campy/P3Steel-MGN-V19-XL/P3Steel XL MGN V19/P3Steel MGN XL/Piezas impresas/LCD Cajas/Duet 5 Pulgadas/Ensamblaje-Duet5.SLDASM

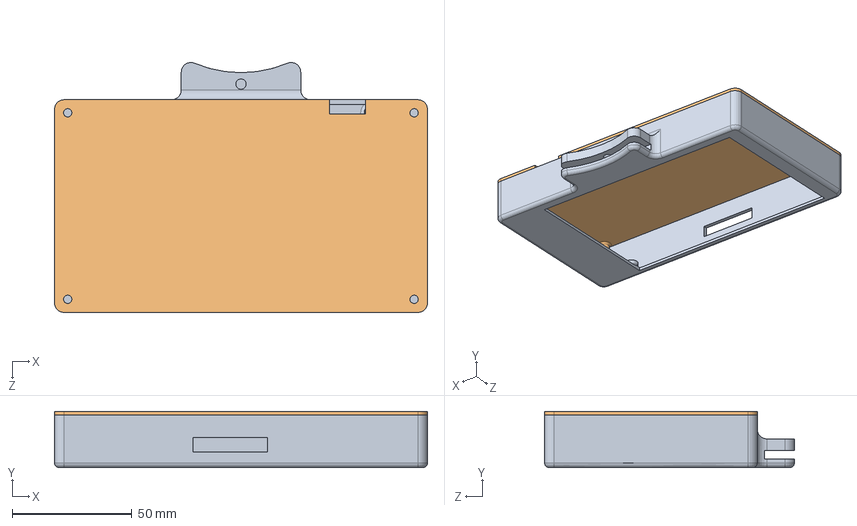
[picture p33: CAD file, 2019-11-12]
P3Steel XL MGN V19/P3Steel MGN XL/Piezas impresas/LCD Cajas/Duet 5 Pulgadas/Ensamblaje-Duet5.SLDASM
156.0 x 23.5 x 104.5 mm
Caja-Duet5
TapaCaja duet 5
