campy/P3Steel-MGN-V19-XL/P3Steel XL MGN V19/P3Steel MGN XL/Source/F688zz/F688ZZ_assembly.SLDASM

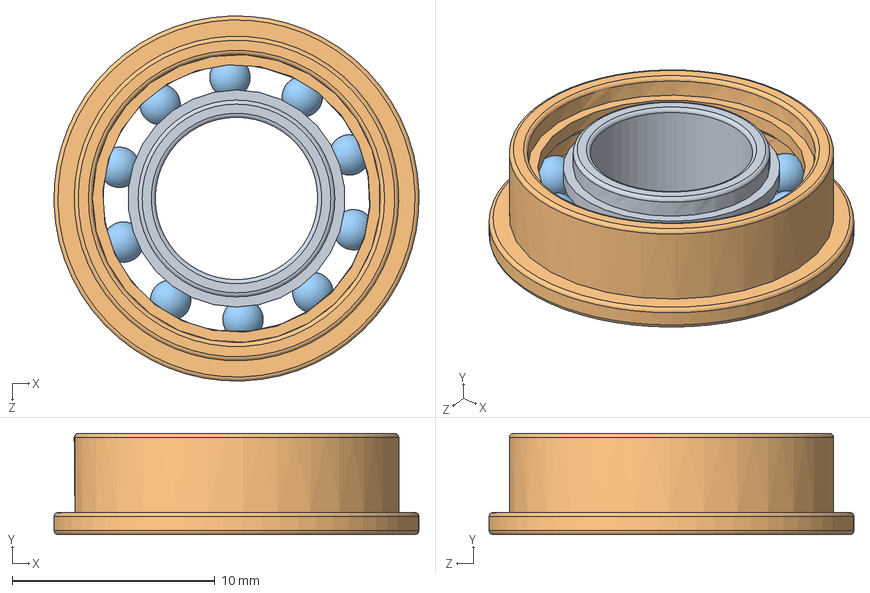
[picture p34: CAD file, 2019-07-11]
P3Steel XL MGN V19/P3Steel MGN XL/Source/F688zz/F688ZZ_assembly.SLDASM
18.0 x 5.00 x 18.0 mm
F688ZZ_shaft
F688ZZ_Housing
F688ZZ_Ball x 10
