campy/P3Steel-MGN-V19-XL/P3Steel XL MGN V19/P3Steel MGN XL/Source/Inductive Sensor/LJ12A3-4-Z.SLDASM

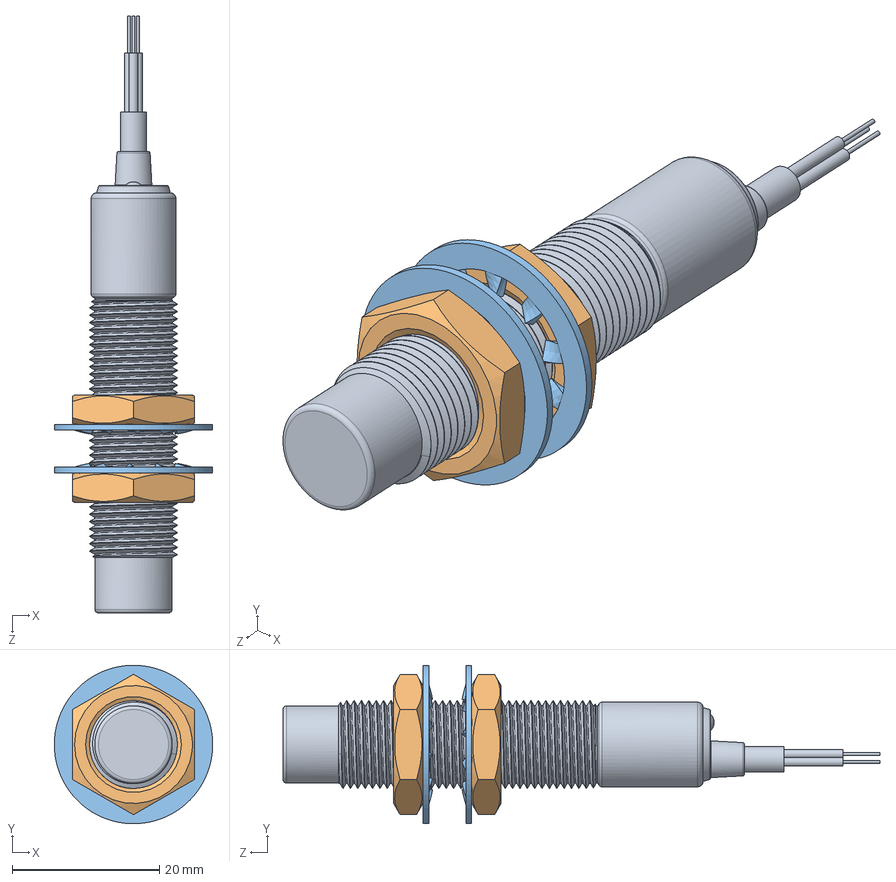
[picture p35: CAD file, 2019-07-11]
P3Steel XL MGN V19/P3Steel MGN XL/Source/Inductive Sensor/LJ12A3-4-Z.SLDASM
21.5 x 21.5 x 81.0 mm
LJ12A3-4-Z
Гайка М12 x 2
Шайба x 2
