campy/P3Steel-MGN-V19-XL/P3Steel XL MGN V19/P3Steel MGN XL/Source/Nema Y/Stepper motor/Nema Z.SLDASM

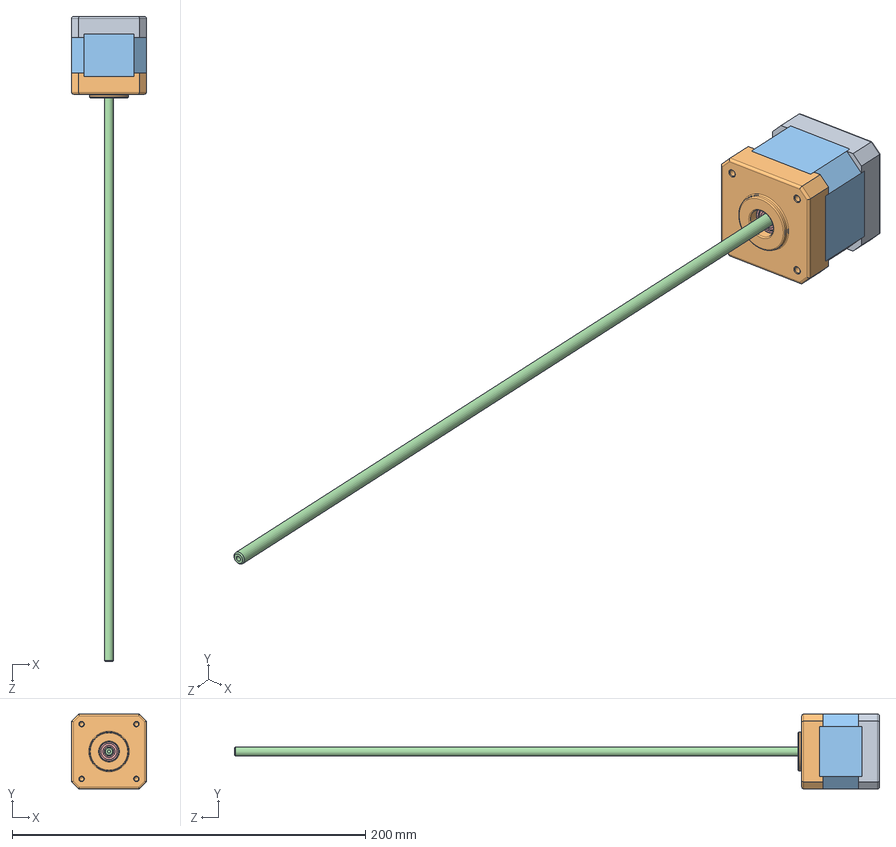
[picture p36: CAD file, 2019-07-11]
P3Steel XL MGN V19/P3Steel MGN XL/Source/Nema Y/Stepper motor/Nema Z.SLDASM
42.3 x 42.3 x 365.0 mm
radial ball bearing_68_iso x 2
pan head cross recess screw_iso x 4
