campy/P3Steel-MGN-V19-XL/P3Steel XL MGN V19/P3Steel MGN XL/Piezas impresas/Cadenetas/Cadeneta 5/Ensamblaje P3steel.SLDASM

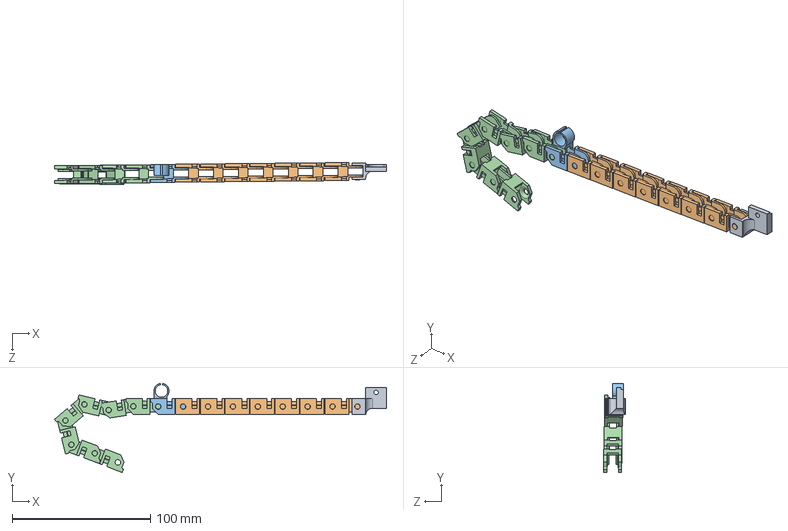
[picture p38: CAD file, 2019-07-11]
P3Steel XL MGN V19/P3Steel MGN XL/Piezas impresas/Cadenetas/Cadeneta 5/Ensamblaje P3steel.SLDASM
240.0 x 64.4 x 15.8 mm
Soporte cama
Eslabon 5 Fijo x 7
Eslabon 5 con soporte
Eslabon 5 Bloqueado x 7
