campy/P3Steel-MGN-V19-XL/P3Steel XL MGN V19/P3Steel MGN XL/Ensamblaje-Xmotor.SLDASM

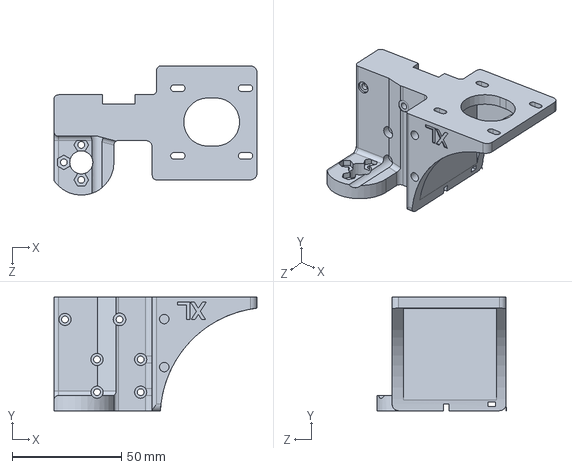
[picture p39: CAD file, 2019-09-07]
P3Steel XL MGN V19/P3Steel MGN XL/Ensamblaje-Xmotor.SLDASM
93.0 x 52.0 x 59.2 mm
