campy/P3Steel-MGN-V19-XL/P3Steel XL MGN V19/P3Steel MGN XL/Extrusor BMG+E3DV6/E3dSimple/fanduct.SLDASM

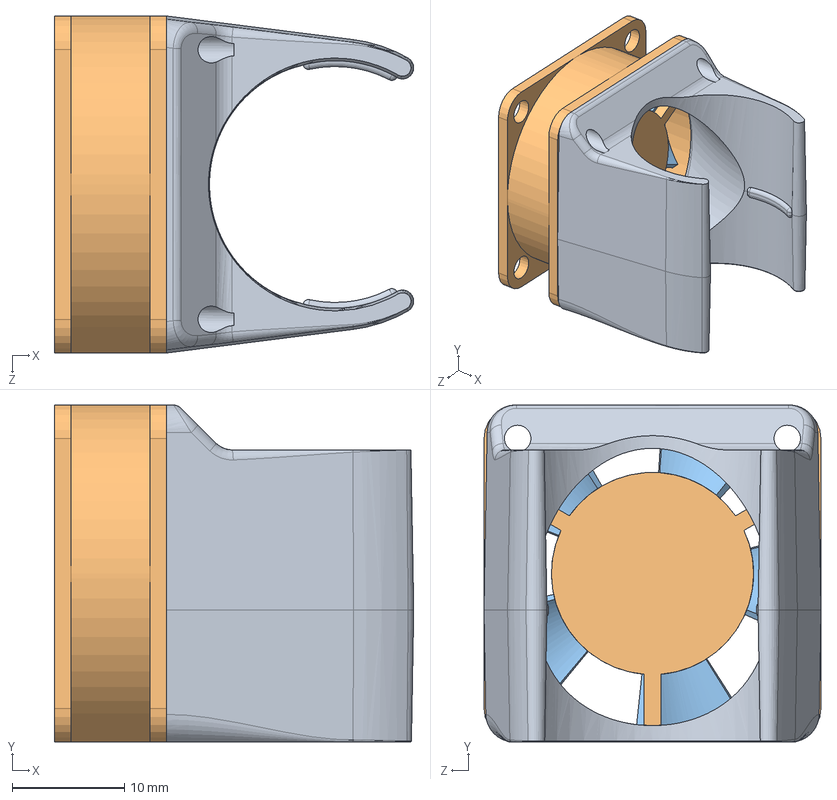
[picture p40: CAD file, 2019-09-07]
P3Steel XL MGN V19/P3Steel MGN XL/Extrusor BMG+E3DV6/E3dSimple/fanduct.SLDASM
32.0 x 30.0 x 30.0 mm
fan duct
fan sub1
fan sub2
