campy/P3Steel-MGN-V19-XL/P3Steel XL MGN V19/P3Steel MGN XL/Piezas impresas/Cadenetas/Cadeneta 15/Ensamblaje Eslabon 15.SLDASM

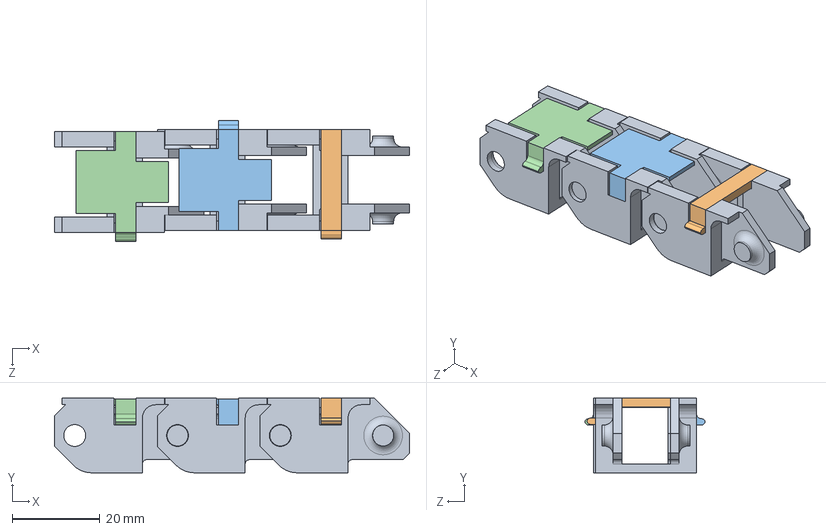
[picture p41: CAD file, 2019-07-11]
P3Steel XL MGN V19/P3Steel MGN XL/Piezas impresas/Cadenetas/Cadeneta 15/Ensamblaje Eslabon 15.SLDASM
80.8 x 17.0 x 27.4 mm
Eslabon 15 x 3
Cierre 15
Cierre 15 Tapa R
Cierre 15 Tapa L
