campy/P3Steel-MGN-V19-XL/P3Steel XL MGN V19/P3Steel MGN XL/Piezas impresas/Cadenetas/Cadeneta 5/Ensamblaje Eslobones.SLDASM

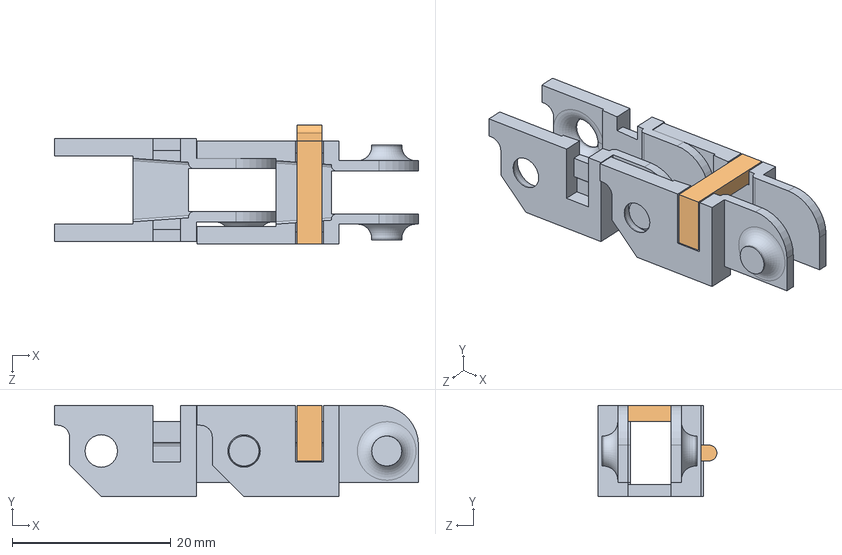
[picture p42: CAD file, 2019-07-11]
P3Steel XL MGN V19/P3Steel MGN XL/Piezas impresas/Cadenetas/Cadeneta 5/Ensamblaje Eslobones.SLDASM
45.9 x 11.5 x 15.0 mm
Eslabon 5 Bloqueado x 2
Cierre 5
