campy/P3Steel-MGN-V19-XL/P3Steel XL MGN V19/P3Steel MGN XL/Piezas impresas/Cadenetas/Cadeneta 5/EnsamblajeBandejaY.SLDASM

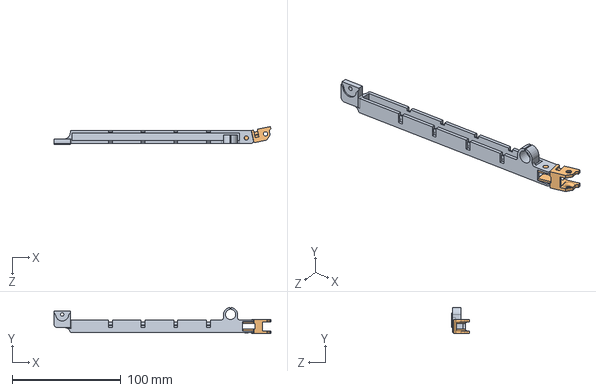
[picture p44: CAD file, 2019-07-11]
P3Steel XL MGN V19/P3Steel MGN XL/Piezas impresas/Cadenetas/Cadeneta 5/EnsamblajeBandejaY.SLDASM
199.1 x 23.9 x 16.5 mm
Soporte Base V2
Eslabon 5 Bloqueado
