campy/P3Steel-MGN-V19-XL/P3Steel XL MGN V19/P3Steel MGN XL/Source/MGN12/MGN12-450.SLDASM

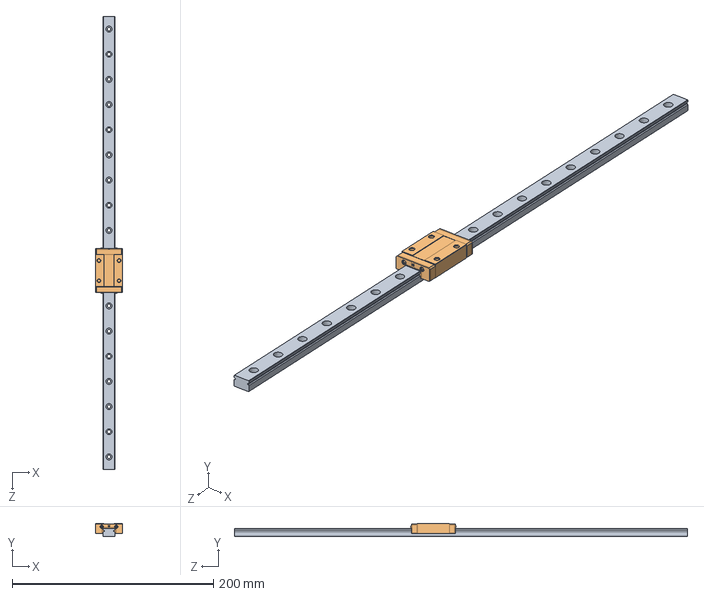
[picture p45: CAD file, 2019-07-11]
P3Steel XL MGN V19/P3Steel MGN XL/Source/MGN12/MGN12-450.SLDASM
27.0 x 13.0 x 450.0 mm
MGN12_450
MGN12-H
