campy/P3Steel-MGN-V19-XL/P3Steel XL MGN V19/P3Steel MGN XL/Source/Titan Aero/Titan Aero P3steel/soportetitan.SLDASM

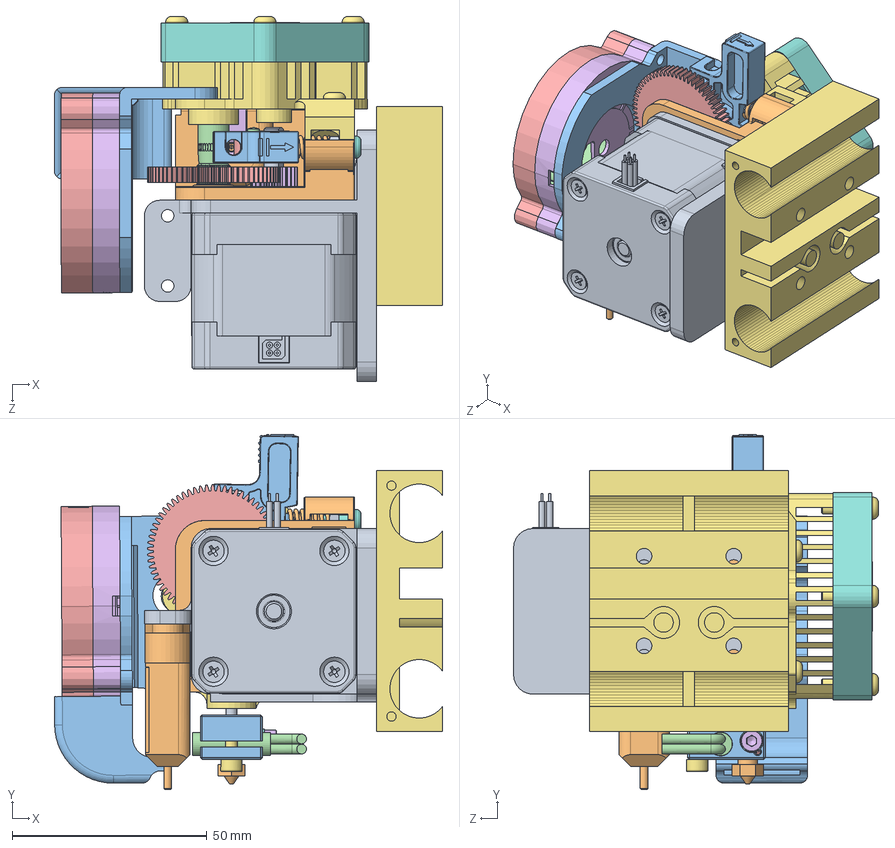
[picture p46: CAD file, 2019-07-11]
P3Steel XL MGN V19/P3Steel MGN XL/Source/Titan Aero/Titan Aero P3steel/soportetitan.SLDASM
99.6 x 91.2 x 93.6 mm
soportetitan
Base
9x5x3mm bearing x 2
hobbed wheel
filament gear
motor gear
cover
m3x8
M3 nut
idler spring
tensioner
idler bearing pin
idler bearing
guide tube
ISO 7380 - M3 x 28 v1 x 8
Fan 40 X 40 X 10 v4
E3D v6 HotEnd - Heatbreak
E3D v6 HotEnd - Nozzle
E3D v6 HotEnd - Heat Block
Ceramic Cartridge Heater
Thermistor
HEXAGON SOCKET HEAD CAP SCREWS_SCB3-4
HEXAGON SOCKET HEAD CAP SCREWS_SCB3-10
Flat Washers_PWF3
17HM15-0904S
BLTouch
tobera5015s
turbine
top
bottom
xcarriage
