campy/P3Steel-MGN-V19-XL/P3Steel XL MGN V19/P3Steel MGN XL/Source/MGN12/17HM15-0904S.SLDASM

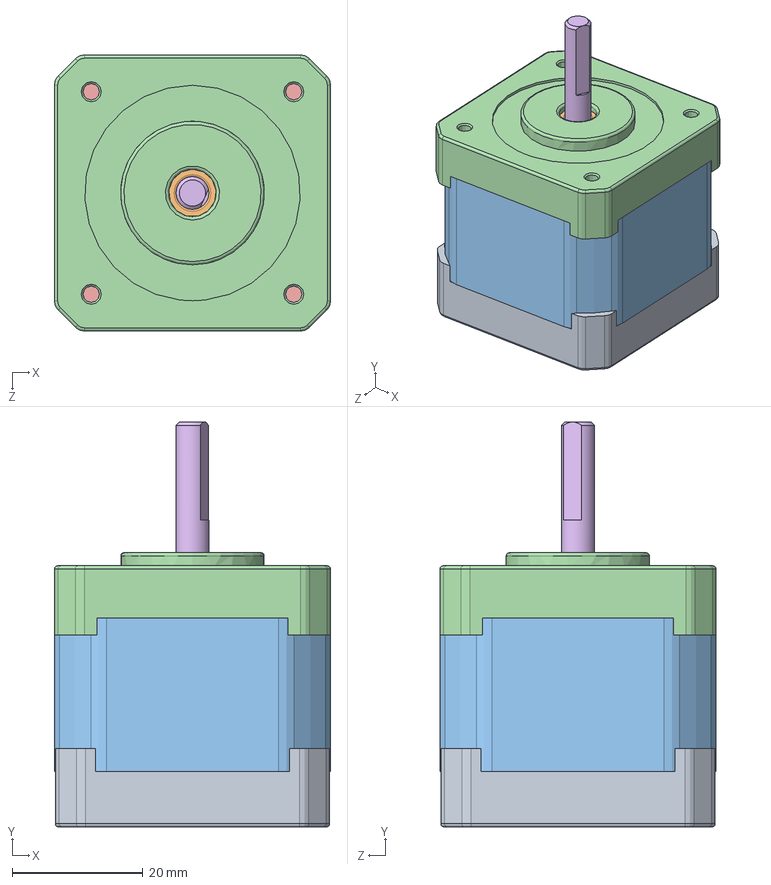
[picture p47: CAD file, 2019-07-11]
P3Steel XL MGN V19/P3Steel MGN XL/Source/MGN12/17HM15-0904S.SLDASM
42.3 x 62.0 x 42.3 mm
nema17_bottom_40mm
radial ball bearing_68_din x 2
nema17_middle_40mm
nema17_top_40mm
countersunk flat head cross recess screw_din x 4
nema17_shaft_40mm
