campy/P3Steel-MGN-V19-XL/P3Steel MGN XL BMG/Piezas impresas/LCD Cajas/Duet 7 Pulgadas/Delantera.STL

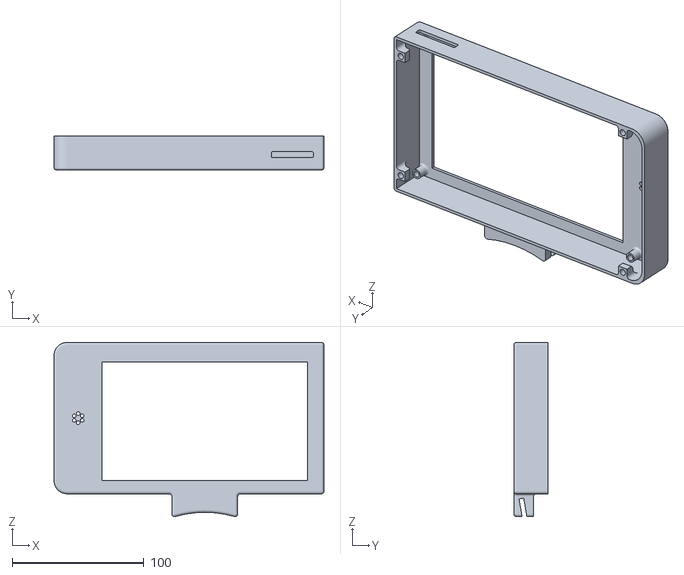
[picture p50: CAD file, 2019-07-11]
P3Steel MGN XL BMG/Piezas impresas/LCD Cajas/Duet 7 Pulgadas/Delantera.STL
205.0 x 26.0 x 132.3
