campy/P3Steel-MGN-V19-XL/P3Steel XL MGN V19/P3Steel MGN XL/Extrusor BMG+E3DV6/E3dSimple/fan sub2.SLDPRT

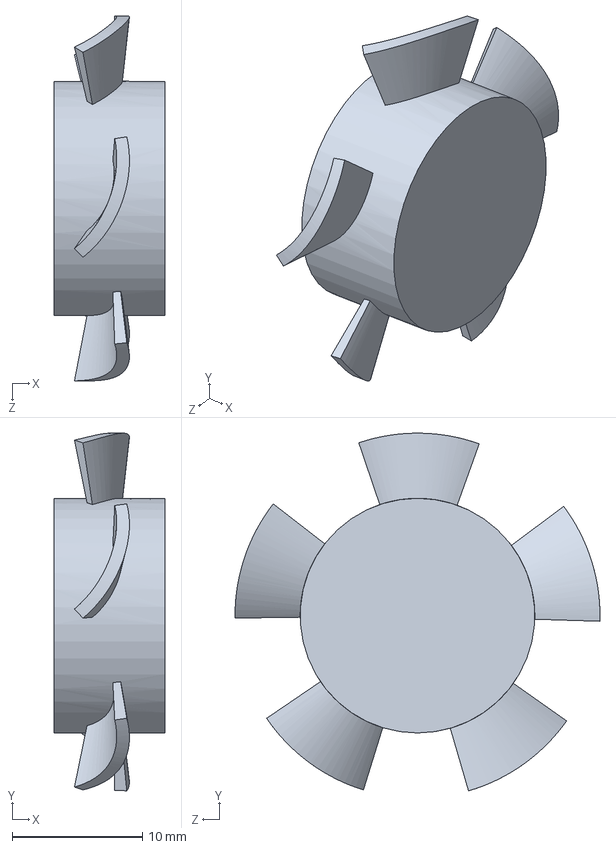
[picture p51: CAD file, 2019-09-07]
P3Steel XL MGN V19/P3Steel MGN XL/Extrusor BMG+E3DV6/E3dSimple/fan sub2.SLDPRT
8.50 x 27.4 x 28.0 mm
