campy/P3Steel-MGN-V19-XL/P3Steel XL MGN V19/P3Steel MGN XL/Extrusor BMG+E3DV6/Nema 17 Corto/Nema 17.SLDPRT

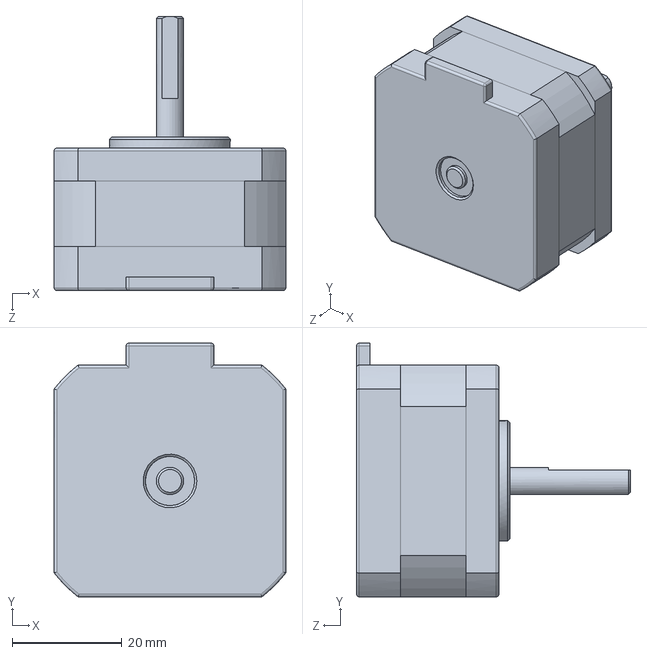
[picture p52: CAD file, 2019-09-07]
P3Steel XL MGN V19/P3Steel MGN XL/Extrusor BMG+E3DV6/Nema 17 Corto/Nema 17.SLDPRT
42.3 x 46.3 x 50.0 mm
