campy/P3Steel-MGN-V19-XL/P3Steel XL MGN V19/P3Steel MGN XL/Extrusor BMG+E3DV6/Radial Cooling Fan 50mm DC12V/top.SLDPRT

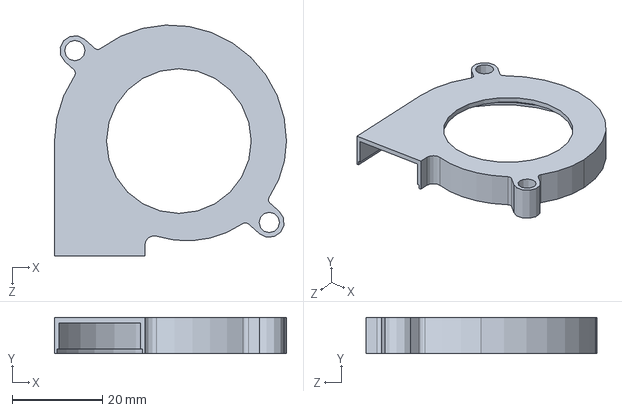
[picture p53: CAD file, 2019-09-07]
P3Steel XL MGN V19/P3Steel MGN XL/Extrusor BMG+E3DV6/Radial Cooling Fan 50mm DC12V/top.SLDPRT
51.3 x 8.00 x 51.0 mm
