campy/P3Steel-MGN-V19-XL/P3Steel XL MGN V19/P3Steel MGN XL/Extrusor BMG+Mosquito/Radial Cooling Fan 50mm DC12V/bottom.SLDPRT

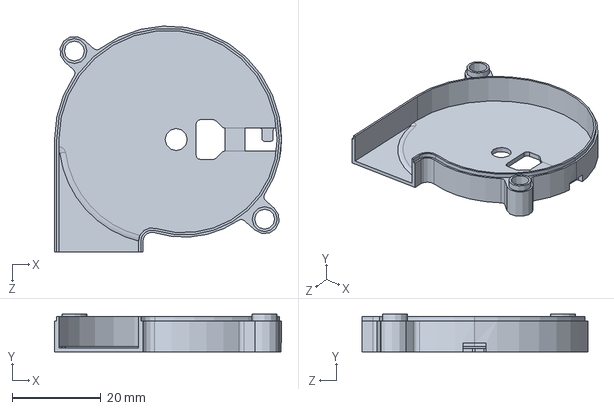
[picture p54: CAD file, 2019-09-07]
P3Steel XL MGN V19/P3Steel MGN XL/Extrusor BMG+Mosquito/Radial Cooling Fan 50mm DC12V/bottom.SLDPRT
51.3 x 8.50 x 51.0 mm
