campy/P3Steel-MGN-V19-XL/P3Steel XL MGN V19/P3Steel MGN XL/Extrusor Titan Aero/Titan Aero/Titan Aero P3steel/Blower titan/Titan_Aero_Shroud_360_Left.stl

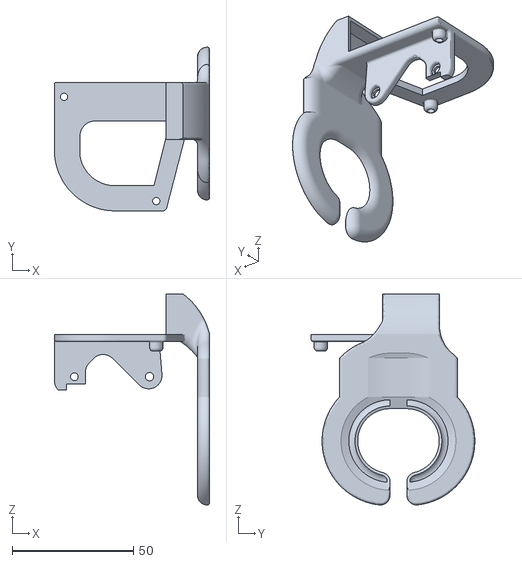
[picture p55: CAD file, 2019-07-11]
P3Steel XL MGN V19/P3Steel MGN XL/Extrusor Titan Aero/Titan Aero/Titan Aero P3steel/Blower titan/Titan_Aero_Shroud_360_Left.stl
64.0 x 67.5 x 87.0
