campy/P3Steel-MGN-V19-XL/P3Steel XL MGN V19/P3Steel MGN XL/Extrusor Titan Aero/X-CarriageV2 Titan.SLDPRT

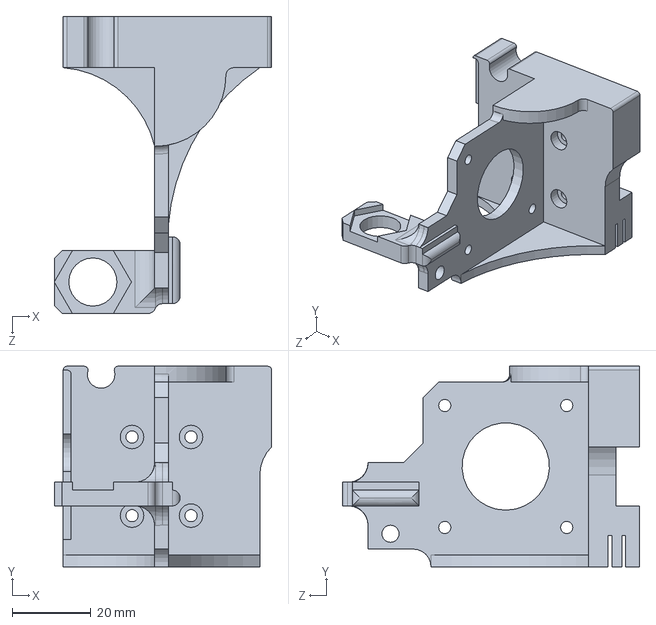
[picture p56: CAD file, 2020-03-17]
P3Steel XL MGN V19/P3Steel MGN XL/Extrusor Titan Aero/X-CarriageV2 Titan.SLDPRT
55.2 x 51.0 x 75.5 mm
