campy/P3Steel-MGN-V19-XL/P3Steel XL MGN V19/P3Steel MGN XL/Marco central XL Offset.SLDPRT

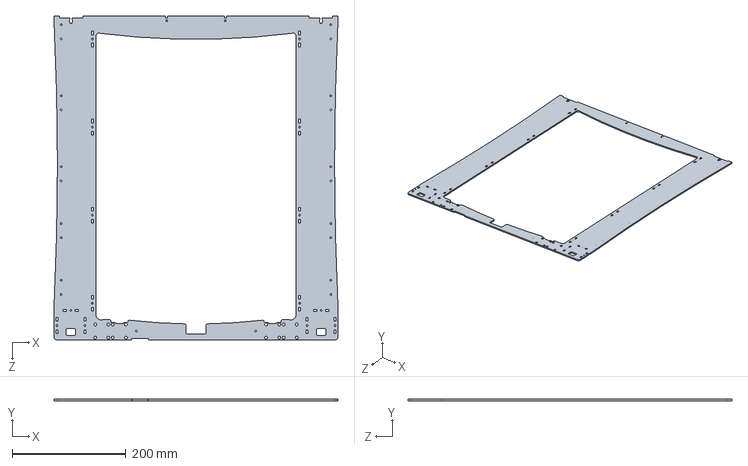
[picture p57: CAD file, 2020-01-10]
P3Steel XL MGN V19/P3Steel MGN XL/Marco central XL Offset.SLDPRT
500.0 x 3.00 x 570.0 mm
