campy/P3Steel-MGN-V19-XL/P3Steel XL MGN V19/P3Steel MGN XL/Piezas impresas/Cadenetas/Cadeneta 15/Otros/Cierre 15.SLDPRT

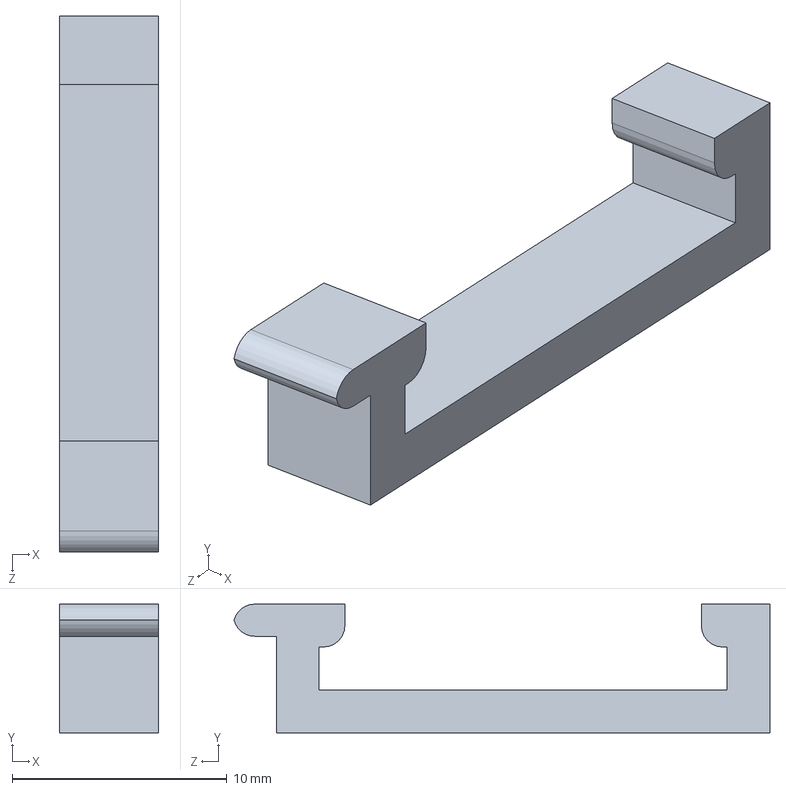
[picture p58: CAD file, 2019-07-11]
P3Steel XL MGN V19/P3Steel MGN XL/Piezas impresas/Cadenetas/Cadeneta 15/Otros/Cierre 15.SLDPRT
4.60 x 6.00 x 25.0 mm
