campy/P3Steel-MGN-V19-XL/P3Steel XL MGN V19/P3Steel MGN XL/Piezas impresas/Cadenetas/Cadeneta 15/Soporte Xcarriage.SLDPRT

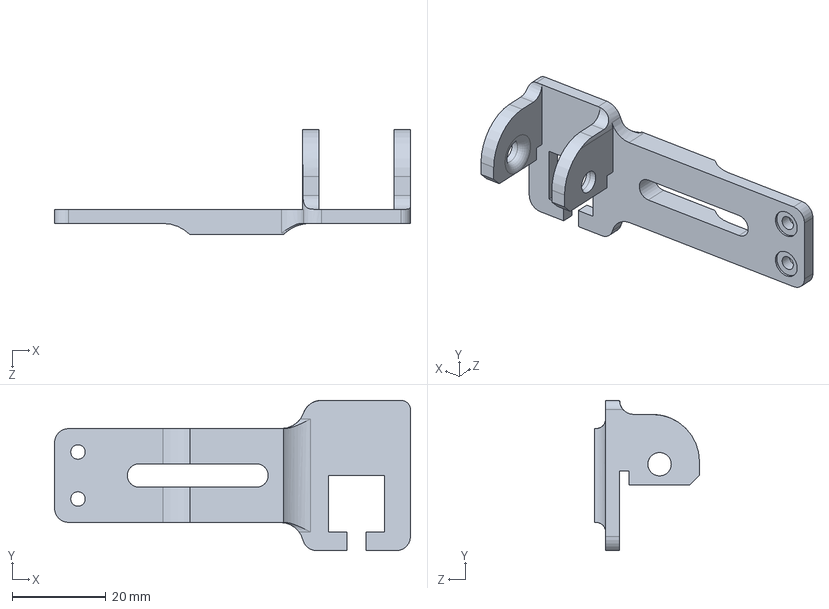
[picture p59: CAD file, 2019-09-07]
P3Steel XL MGN V19/P3Steel MGN XL/Piezas impresas/Cadenetas/Cadeneta 15/Soporte Xcarriage.SLDPRT
75.8 x 32.0 x 22.4 mm
