campy/P3Steel-MGN-V19-XL/P3Steel XL MGN V19/P3Steel MGN XL/Piezas impresas/Cadenetas/Cadeneta 5/Otros Tipos Eslabones/Eslabon 5 Fijo.SLDPRT

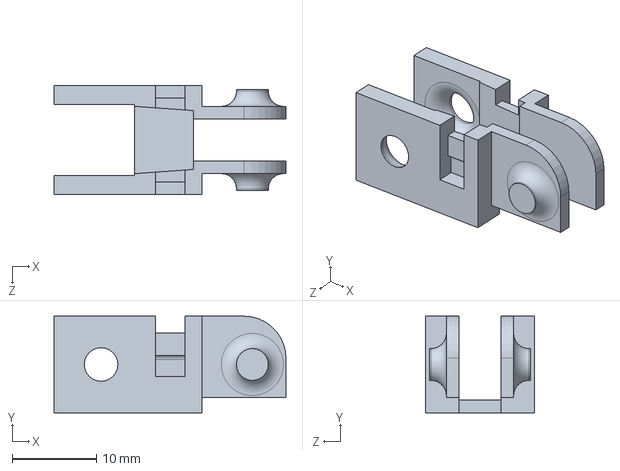
[picture p60: CAD file, 2019-07-11]
P3Steel XL MGN V19/P3Steel MGN XL/Piezas impresas/Cadenetas/Cadeneta 5/Otros Tipos Eslabones/Eslabon 5 Fijo.SLDPRT
27.6 x 11.5 x 13.0 mm
