campy/P3Steel-MGN-V19-XL/P3Steel XL MGN V19/P3Steel MGN XL/Piezas impresas/Cadenetas/Cadeneta 5/Soporte electronica V2.SLDPRT

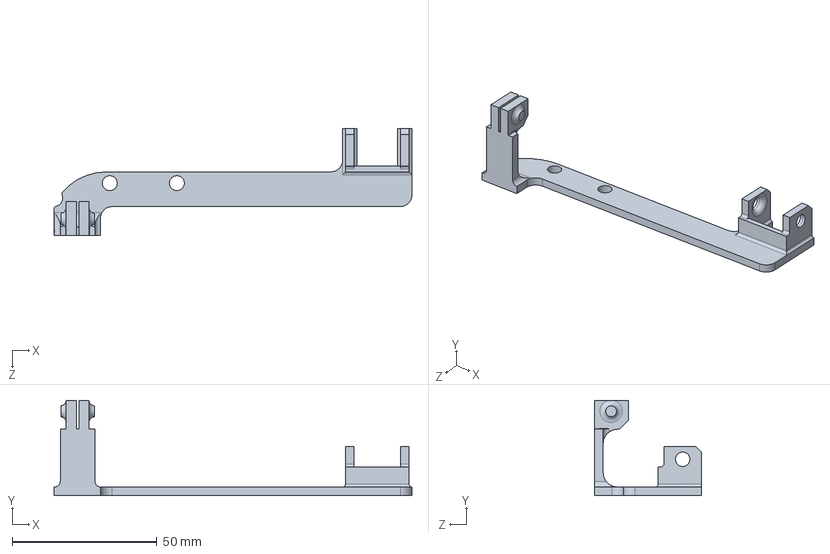
[picture p61: CAD file, 2019-10-11]
P3Steel XL MGN V19/P3Steel MGN XL/Piezas impresas/Cadenetas/Cadeneta 5/Soporte electronica V2.SLDPRT
123.8 x 33.0 x 37.0 mm
