campy/P3Steel-MGN-V19-XL/P3Steel XL MGN V19/P3Steel MGN XL/Piezas impresas/F-Sensor/Sensor con endstop/Soporte F-Sensor.SLDPRT

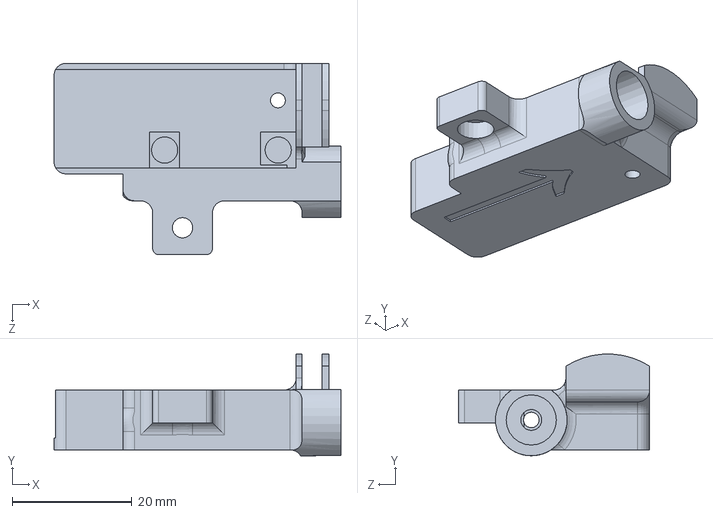
[picture p62: CAD file, 2019-07-11]
P3Steel XL MGN V19/P3Steel MGN XL/Piezas impresas/F-Sensor/Sensor con endstop/Soporte F-Sensor.SLDPRT
48.0 x 17.0 x 32.0 mm
