campy/P3Steel-MGN-V19-XL/P3Steel XL MGN V19/P3Steel MGN XL/Piezas impresas/LCD Cajas/Duet 5 Pulgadas/Caja-Duet5.sldprt

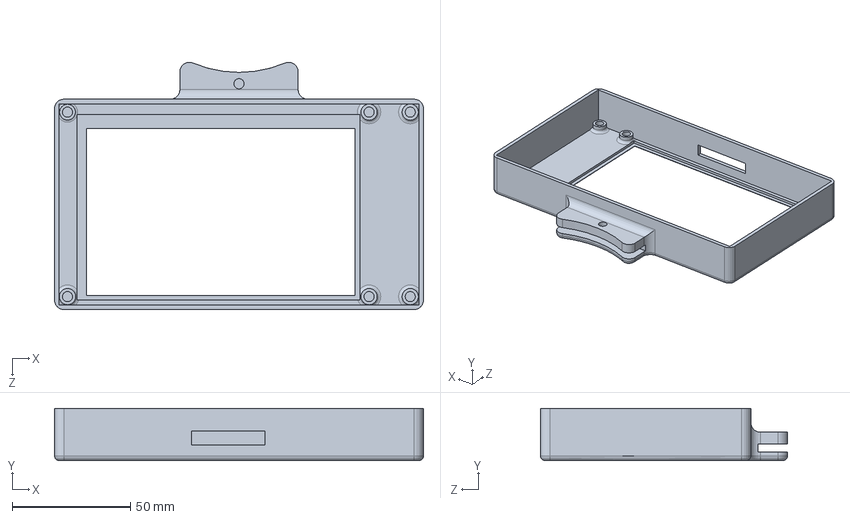
[picture p63: CAD file, 2019-11-12]
P3Steel XL MGN V19/P3Steel MGN XL/Piezas impresas/LCD Cajas/Duet 5 Pulgadas/Caja-Duet5.sldprt
156.0 x 22.0 x 104.5 mm
