campy/P3Steel-MGN-V19-XL/P3Steel XL MGN V19/P3Steel MGN XL/Piezas impresas/LCD Cajas/Grapa LCD2.SLDPRT

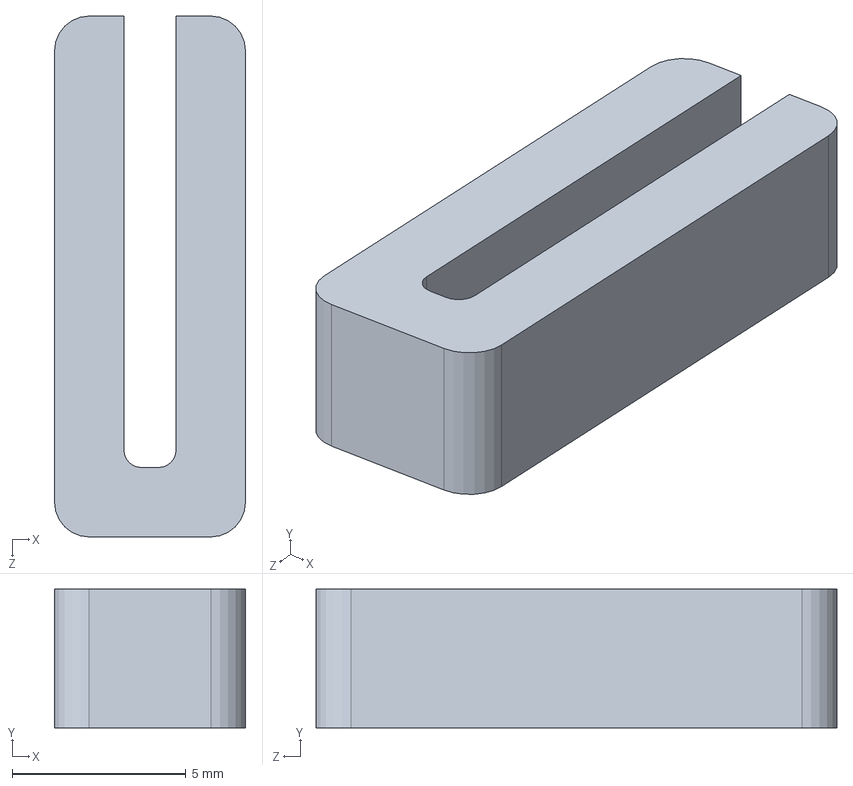
[picture p64: CAD file, 2019-07-11]
P3Steel XL MGN V19/P3Steel MGN XL/Piezas impresas/LCD Cajas/Grapa LCD2.SLDPRT
5.50 x 4.00 x 15.0 mm
