campy/P3Steel-MGN-V19-XL/P3Steel XL MGN V19/P3Steel MGN XL/Piezas impresas/LCD Cajas/Mini 12864 RGB inferior/Mini12864inferior.SLDPRT

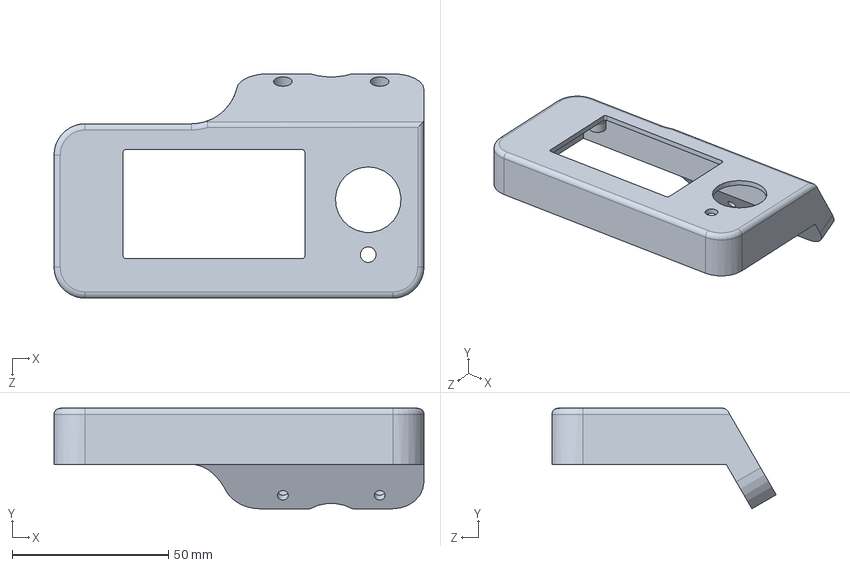
[picture p65: CAD file, 2020-01-10]
P3Steel XL MGN V19/P3Steel MGN XL/Piezas impresas/LCD Cajas/Mini 12864 RGB inferior/Mini12864inferior.SLDPRT
118.5 x 32.2 x 71.9 mm
