campy/P3Steel-MGN-V19-XL/P3Steel XL MGN V19/P3Steel MGN XL/Piezas impresas/LCD Cajas/Mini 12864 RGB V1.2/Mini 12864 Multi-material/D.STL

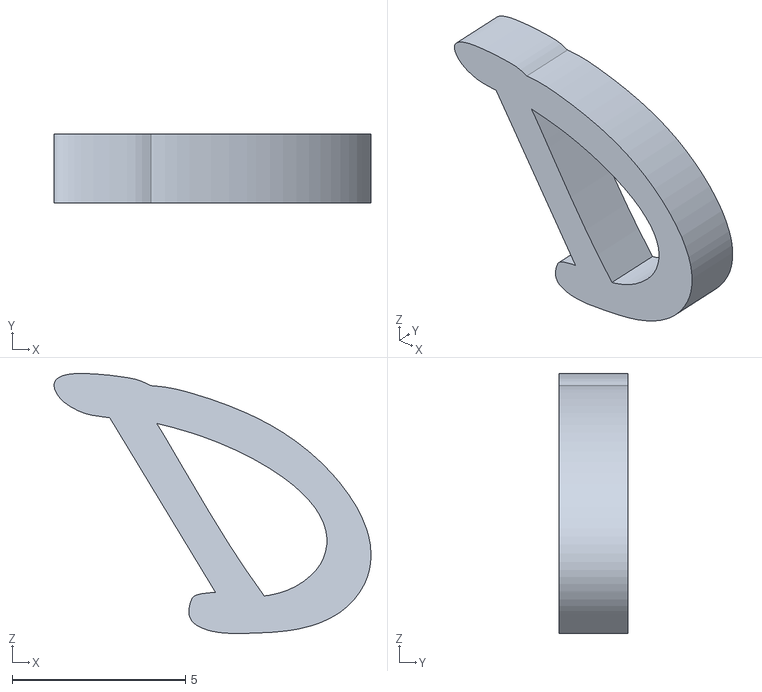
[picture p66: CAD file, 2019-09-07]
P3Steel XL MGN V19/P3Steel MGN XL/Piezas impresas/LCD Cajas/Mini 12864 RGB V1.2/Mini 12864 Multi-material/D.STL
9.15 x 2.00 x 7.51
