campy/P3Steel-MGN-V19-XL/P3Steel XL MGN V19/P3Steel MGN XL/Piezas impresas/LCD Cajas/Mini 12864 RGB V1.2/Mini12864.SLDPRT

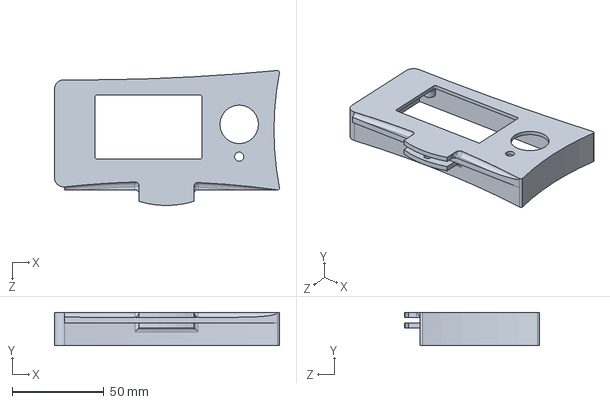
[picture p67: CAD file, 2019-09-07]
P3Steel XL MGN V19/P3Steel MGN XL/Piezas impresas/LCD Cajas/Mini 12864 RGB V1.2/Mini12864.SLDPRT
122.6 x 18.0 x 73.6 mm
