campy/P3Steel-MGN-V19-XL/P3Steel XL MGN V19/P3Steel MGN XL/Piezas impresas/LCD Cajas/MKS12864 Soporte Marco/LCD Tapa support.STL

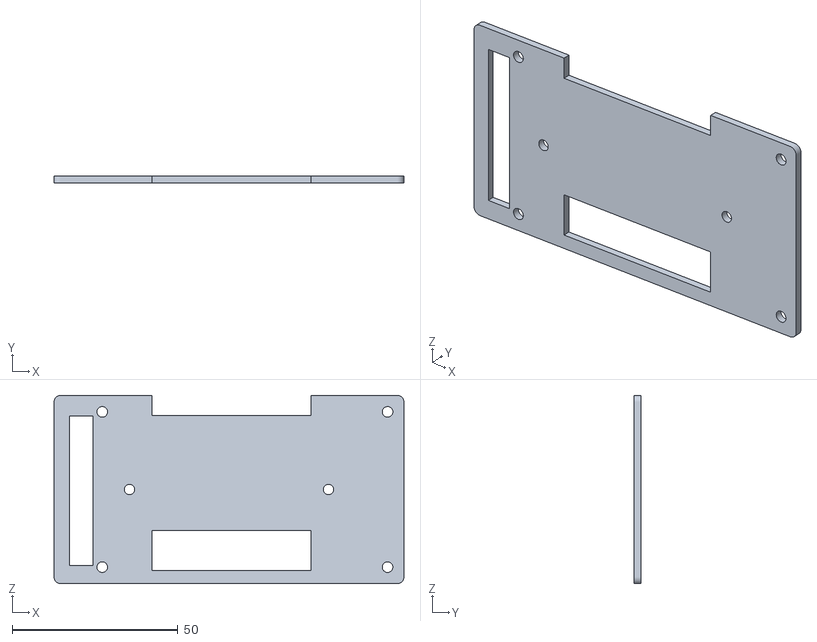
[picture p68: CAD file, 2019-07-11]
P3Steel XL MGN V19/P3Steel MGN XL/Piezas impresas/LCD Cajas/MKS12864 Soporte Marco/LCD Tapa support.STL
105.5 x 2.00 x 56.7
