campy/P3Steel-MGN-V19-XL/P3Steel XL MGN V19/P3Steel MGN XL/Piezas impresas/LCD Cajas/TFT 3.5 2en1/tapa.SLDPRT

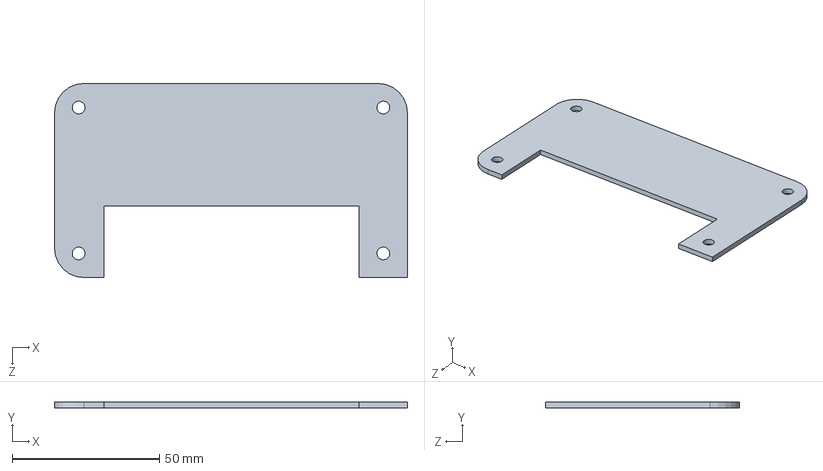
[picture p70: CAD file, 2020-03-17]
P3Steel XL MGN V19/P3Steel MGN XL/Piezas impresas/LCD Cajas/TFT 3.5 2en1/tapa.SLDPRT
120.0 x 2.00 x 66.0 mm
