campy/P3Steel-MGN-V19-XL/P3Steel XL MGN V19/P3Steel MGN XL/Piezas impresas/Protectores ventiladores/40mm_crosshair_reduced_fan_cover.stl

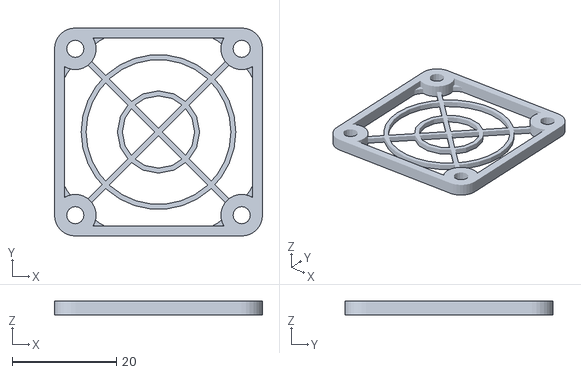
[picture p71: CAD file, 2019-07-11]
P3Steel XL MGN V19/P3Steel MGN XL/Piezas impresas/Protectores ventiladores/40mm_crosshair_reduced_fan_cover.stl
40.0 x 40.0 x 2.70
