campy/P3Steel-MGN-V19-XL/P3Steel XL MGN V19/P3Steel MGN XL/Piezas impresas/Soporte Mot Y XL.SLDPRT

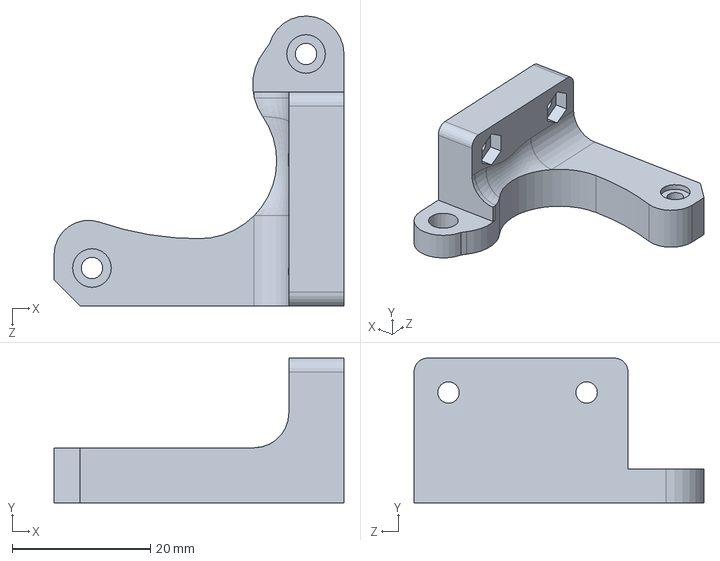
[picture p72: CAD file, 2020-03-17]
P3Steel XL MGN V19/P3Steel MGN XL/Piezas impresas/Soporte Mot Y XL.SLDPRT
42.0 x 21.0 x 42.0 mm
