campy/P3Steel-MGN-V19-XL/P3Steel XL MGN V19/P3Steel MGN XL/Piezas impresas/Soportes electronicas/Caja MKS SKR/MksGenL Abierta.SLDPRT

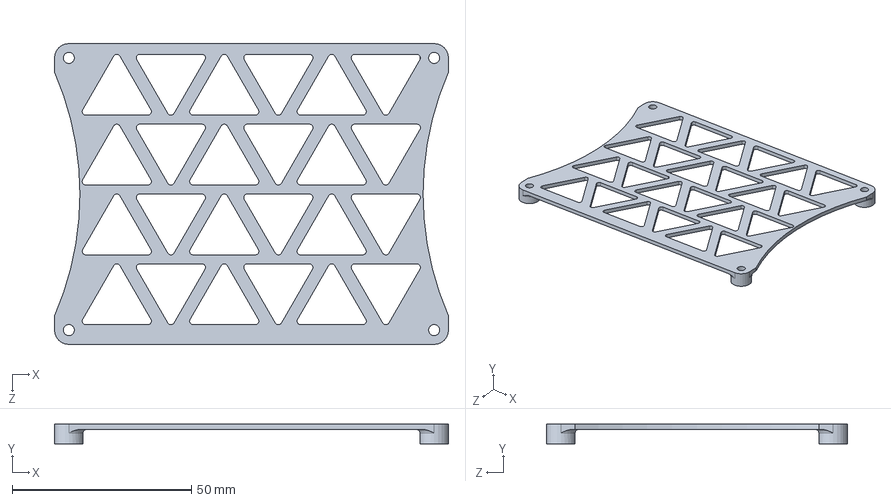
[picture p73: CAD file, 2019-07-11]
P3Steel XL MGN V19/P3Steel MGN XL/Piezas impresas/Soportes electronicas/Caja MKS SKR/MksGenL Abierta.SLDPRT
110.0 x 5.50 x 84.0 mm
