campy/P3Steel-MGN-V19-XL/P3Steel XL MGN V19/P3Steel MGN XL/Piezas impresas/Soportes electronicas/Placas/MKS Gen L/Makerbase GEN.SLDPRT

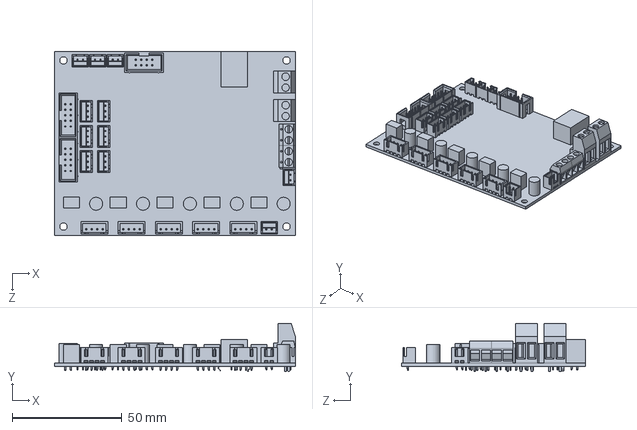
[picture p74: CAD file, 2019-09-07]
P3Steel XL MGN V19/P3Steel MGN XL/Piezas impresas/Soportes electronicas/Placas/MKS Gen L/Makerbase GEN.SLDPRT
110.0 x 22.1 x 84.0 mm
