campy/P3Steel-MGN-V19-XL/P3Steel XL MGN V19/P3Steel MGN XL/Piezas impresas/Soportes electronicas/Placas/Raspi3B+_Mock.SLDPRT

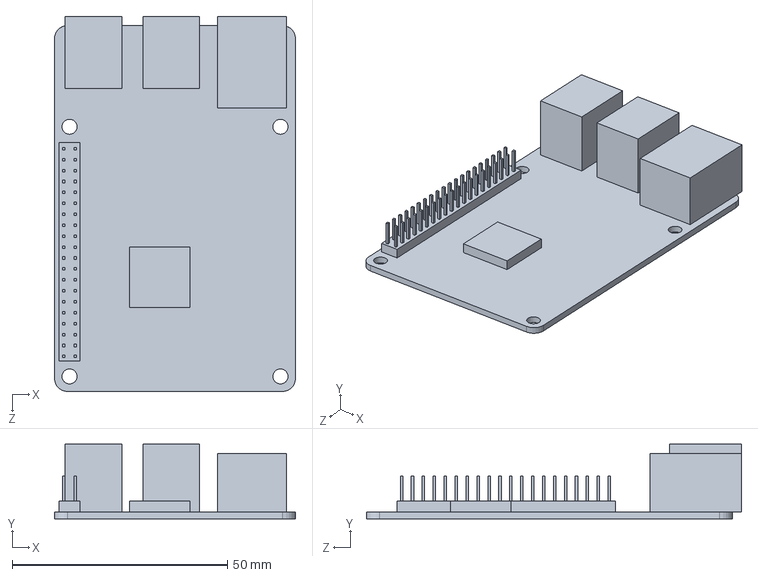
[picture p75: CAD file, 2019-09-07]
P3Steel XL MGN V19/P3Steel MGN XL/Piezas impresas/Soportes electronicas/Placas/Raspi3B+_Mock.SLDPRT
56.0 x 17.4 x 87.1 mm
