campy/P3Steel-MGN-V19-XL/P3Steel XL MGN V19/P3Steel MGN XL/Piezas impresas/Soportes electronicas/Soporte Raspberry.SLDPRT

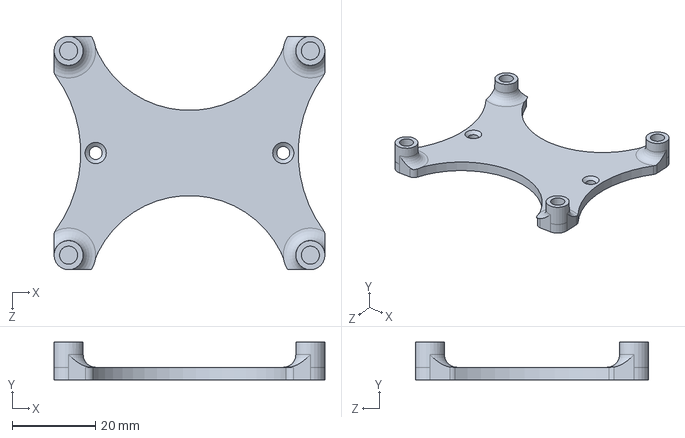
[picture p76: CAD file, 2019-09-07]
P3Steel XL MGN V19/P3Steel MGN XL/Piezas impresas/Soportes electronicas/Soporte Raspberry.SLDPRT
65.0 x 9.00 x 56.0 mm
