campy/P3Steel-MGN-V19-XL/P3Steel XL MGN V19/P3Steel MGN XL/Piezas impresas/Soportes electronicas/Tapa Electronica/Tapa Electronica Duet ETH.SLDPRT

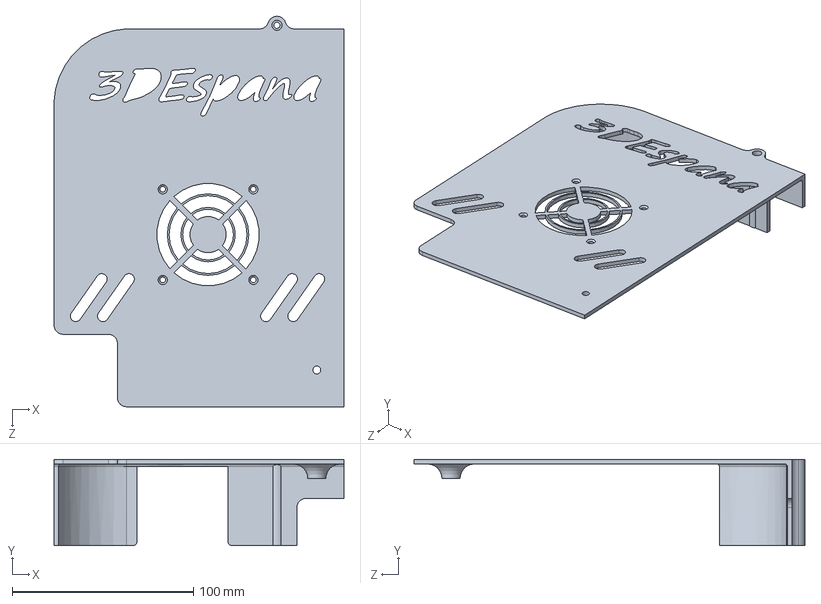
[picture p77: CAD file, 2020-01-10]
P3Steel XL MGN V19/P3Steel MGN XL/Piezas impresas/Soportes electronicas/Tapa Electronica/Tapa Electronica Duet ETH.SLDPRT
160.0 x 47.5 x 215.5 mm
