campy/P3Steel-MGN-V19-XL/P3Steel XL MGN V19/P3Steel MGN XL/Piezas impresas/Soportes electronicas/Tapa Electronica/Tapa multi/rejilla 2.STL

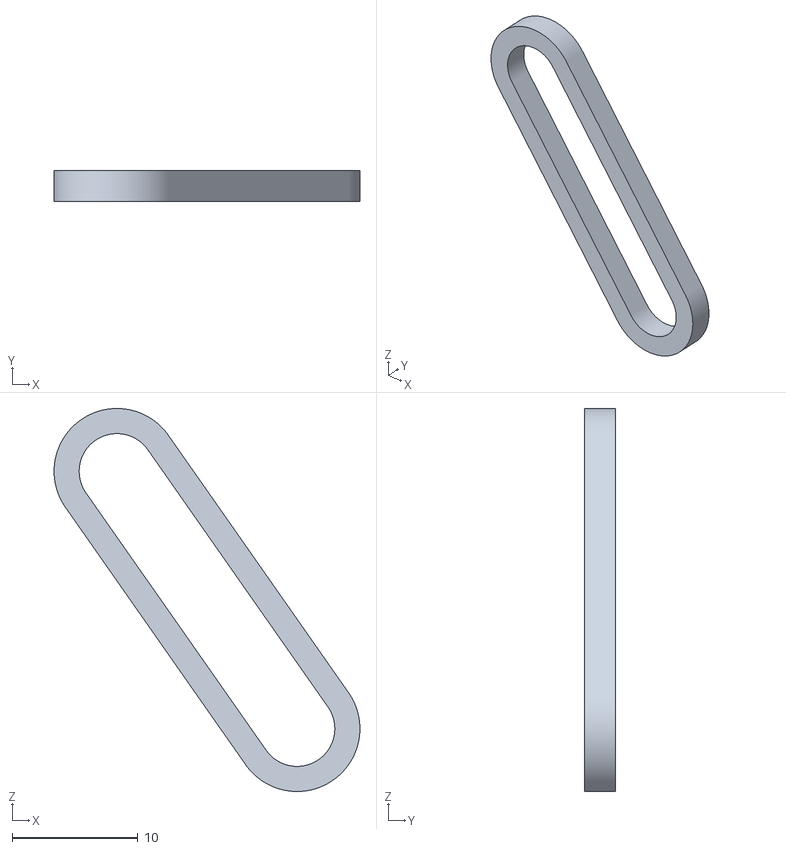
[picture p78: CAD file, 2019-09-07]
P3Steel XL MGN V19/P3Steel MGN XL/Piezas impresas/Soportes electronicas/Tapa Electronica/Tapa multi/rejilla 2.STL
24.3 x 2.50 x 30.5
