campy/P3Steel-MGN-V19-XL/P3Steel XL MGN V19/P3Steel MGN XL/Piezas impresas/Spool holder V2/Soporte filamento con 608zz/spulenhalter_links.stp

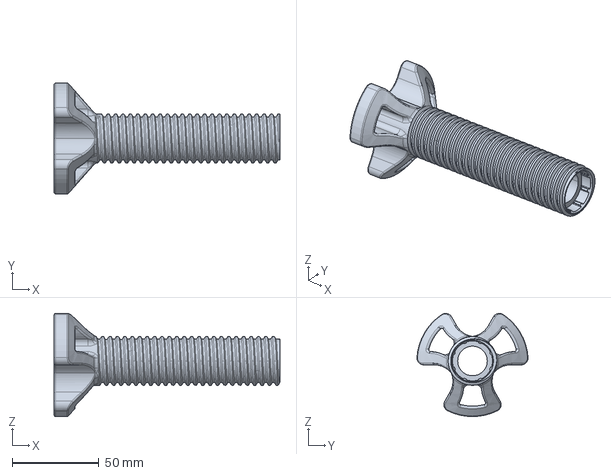
[picture p79: CAD file, 2020-03-17]
P3Steel XL MGN V19/P3Steel MGN XL/Piezas impresas/Spool holder V2/Soporte filamento con 608zz/spulenhalter_links.stp
130.0 x 63.9 x 59.3 mm
