campy/P3Steel-MGN-V19-XL/P3Steel XL MGN V19/P3Steel MGN XL/Piezas impresas/Spool holder V2/Tapon tuerca.SLDPRT

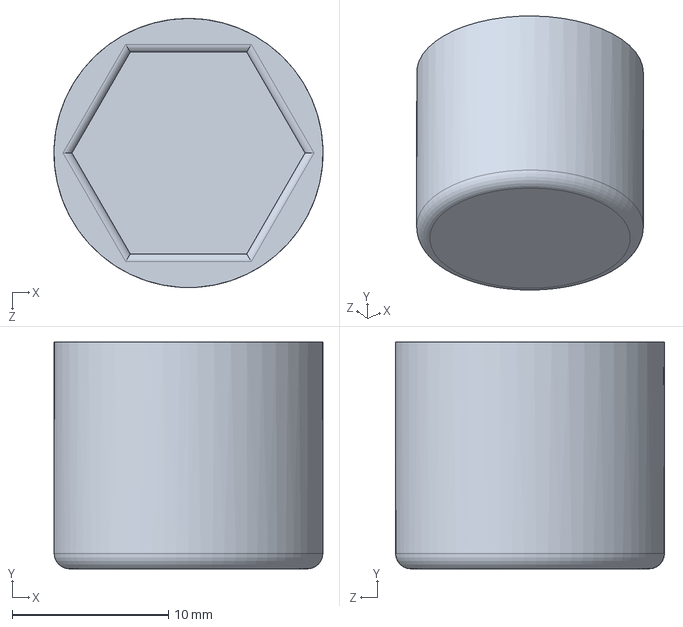
[picture p80: CAD file, 2020-03-17]
P3Steel XL MGN V19/P3Steel MGN XL/Piezas impresas/Spool holder V2/Tapon tuerca.SLDPRT
17.2 x 14.5 x 17.2 mm
