campy/P3Steel-MGN-V19-XL/P3Steel XL MGN V19/P3Steel MGN XL/Piezas impresas/Tapas perfiles/Tapa Trasera.SLDPRT

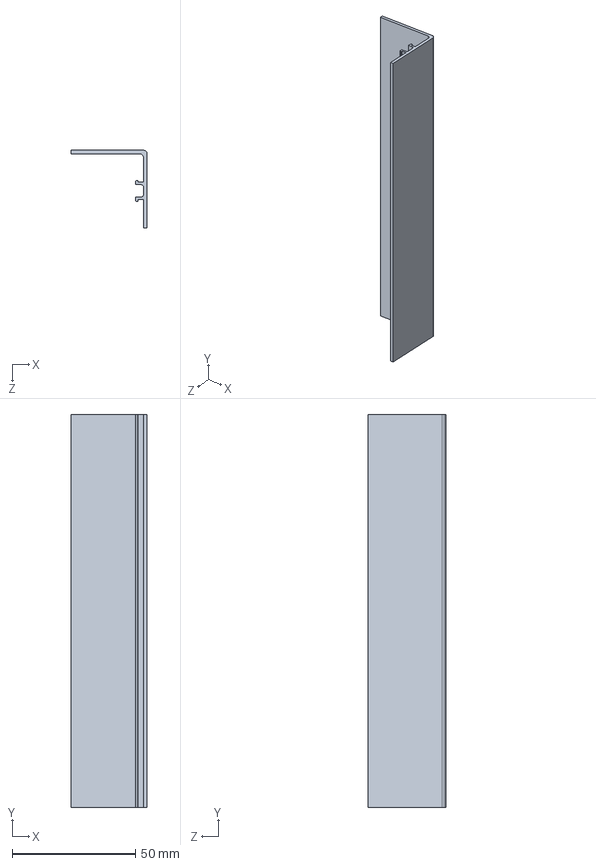
[picture p81: CAD file, 2019-09-13]
P3Steel XL MGN V19/P3Steel MGN XL/Piezas impresas/Tapas perfiles/Tapa Trasera.SLDPRT
31.0 x 159.5 x 31.5 mm
