campy/P3Steel-MGN-V19-XL/P3Steel XL MGN V19/P3Steel MGN XL/Source/3mm Pulley/PULLEY 16T GT-2.SLDPRT

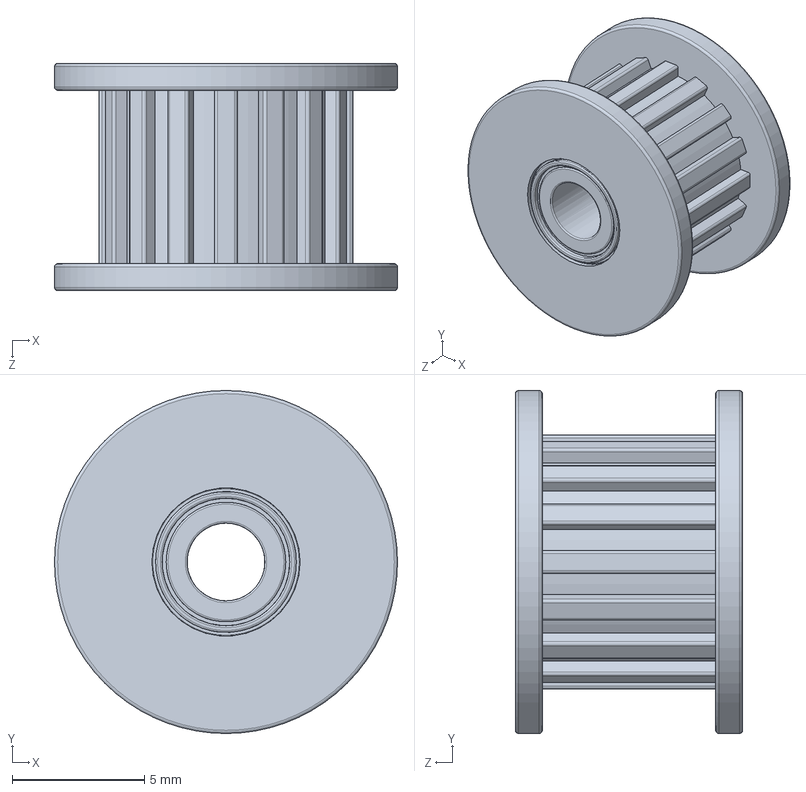
[picture p82: CAD file, 2019-09-07]
P3Steel XL MGN V19/P3Steel MGN XL/Source/3mm Pulley/PULLEY 16T GT-2.SLDPRT
13.0 x 13.0 x 8.59 mm
