campy/P3Steel-MGN-V19-XL/P3Steel XL MGN V19/P3Steel MGN XL/Source/BMG/BMG_Extruder v3.sldprt

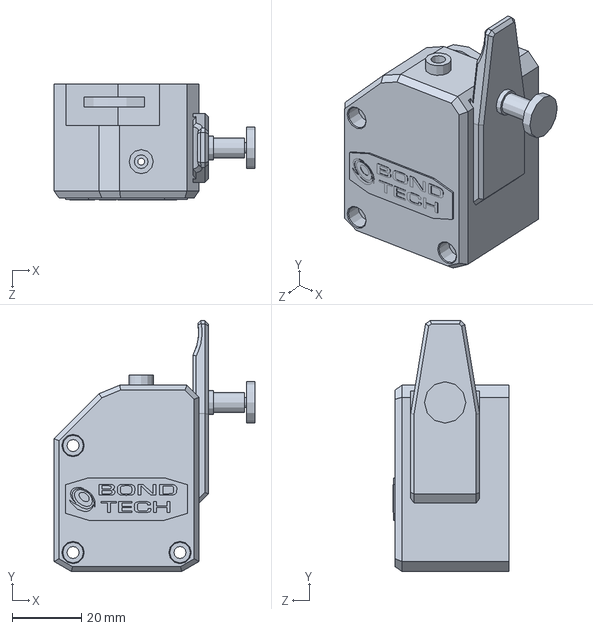
[picture p83: CAD file, 2019-09-07]
P3Steel XL MGN V19/P3Steel MGN XL/Source/BMG/BMG_Extruder v3.sldprt
58.2 x 72.8 x 33.6 mm
