campy/P3Steel-MGN-V19-XL/P3Steel XL MGN V19/P3Steel MGN XL/Source/Conector C14/blade_12.SLDPRT

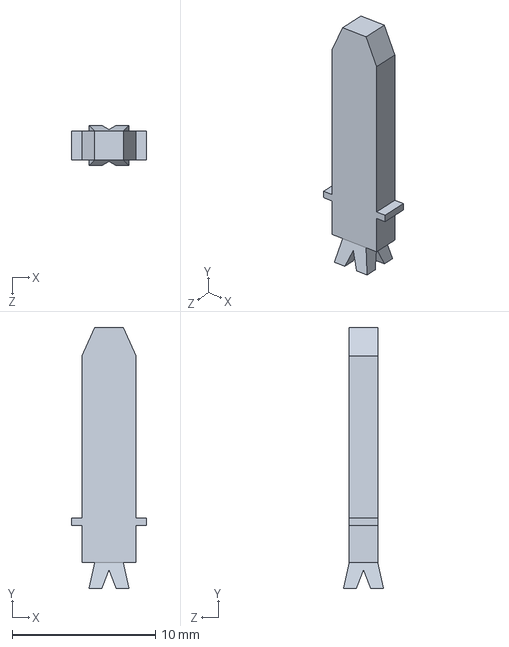
[picture p84: CAD file, 2019-09-07]
P3Steel XL MGN V19/P3Steel MGN XL/Source/Conector C14/blade_12.SLDPRT
5.25 x 18.2 x 2.80 mm
