campy/P3Steel-MGN-V19-XL/P3Steel XL MGN V19/P3Steel MGN XL/Source/Coupler/Shaft Coupler 8-5mm.SLDPRT

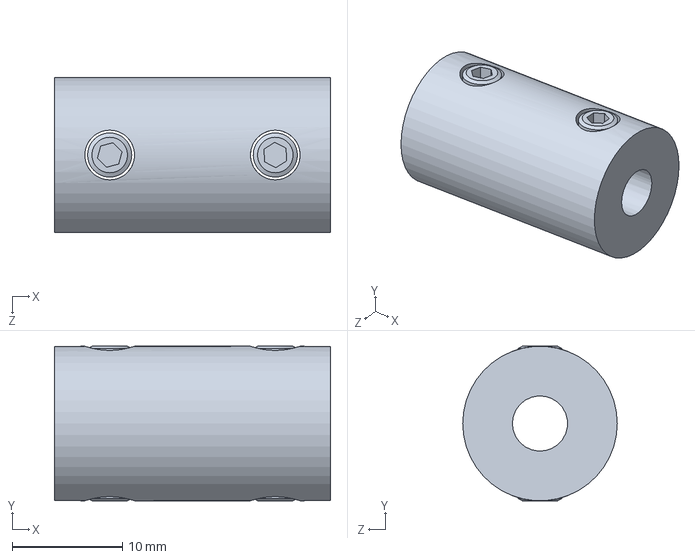
[picture p85: CAD file, 2019-09-07]
P3Steel XL MGN V19/P3Steel MGN XL/Source/Coupler/Shaft Coupler 8-5mm.SLDPRT
25.0 x 14.0 x 14.0 mm
