campy/P3Steel-MGN-V19-XL/P3Steel XL MGN V19/P3Steel MGN XL/Source/F688zz/F688ZZ_Housing.SLDPRT

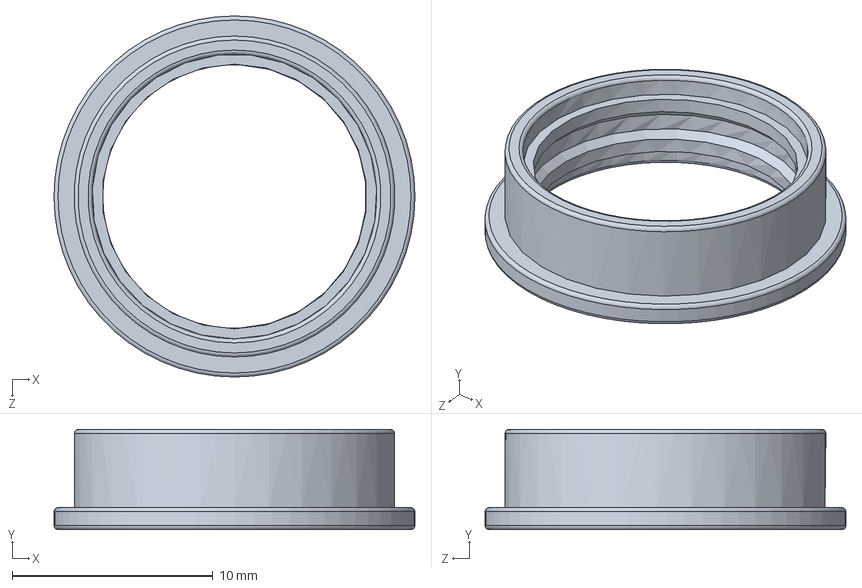
[picture p86: CAD file, 2019-07-11]
P3Steel XL MGN V19/P3Steel MGN XL/Source/F688zz/F688ZZ_Housing.SLDPRT
18.0 x 5.00 x 18.0 mm
