campy/P3Steel-MGN-V19-XL/P3Steel XL MGN V19/P3Steel MGN XL/Source/Inductive Sensor/Гайка М12.SLDPRT

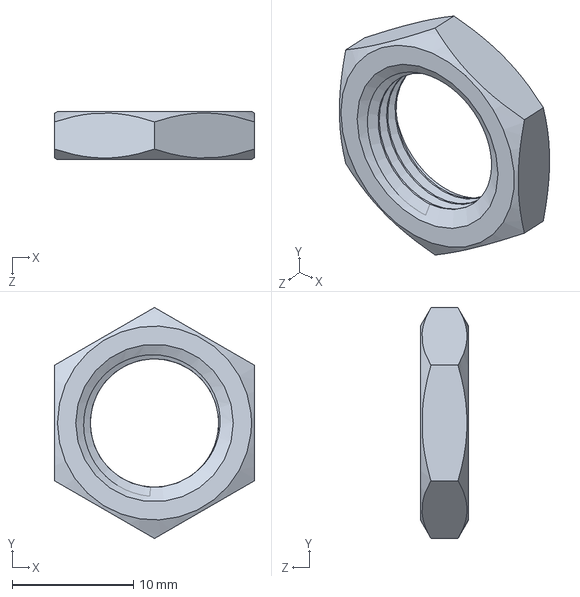
[picture p87: CAD file, 2019-09-07]
P3Steel XL MGN V19/P3Steel MGN XL/Source/Inductive Sensor/Гайка М12.SLDPRT
16.5 x 19.1 x 4.00 mm
