campy/P3Steel-MGN-V19-XL/P3Steel XL MGN V19/P3Steel MGN XL/Source/LCD/MKS mini LCD.IGS

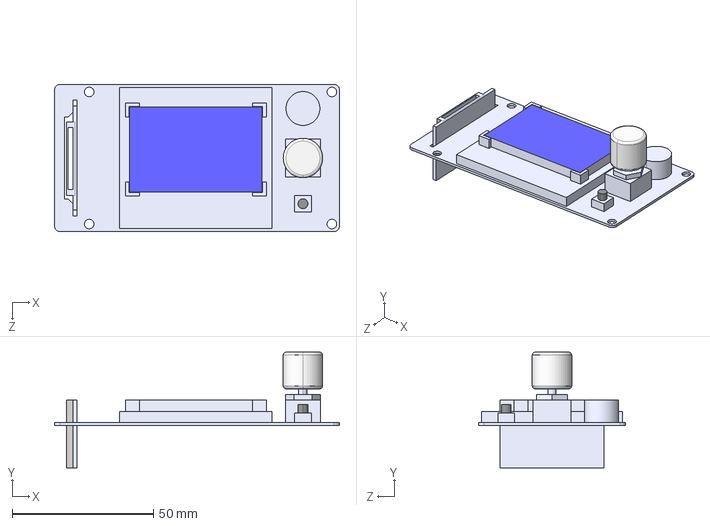
[picture p88: CAD file, 2019-07-11]
P3Steel XL MGN V19/P3Steel MGN XL/Source/LCD/MKS mini LCD.IGS
101.0 x 41.0 x 52.2 mm
