campy/P3Steel-MGN-V19-XL/P3Steel XL MGN V19/P3Steel MGN XL/Source/MGN12C300/MGN12C300.SLDPRT

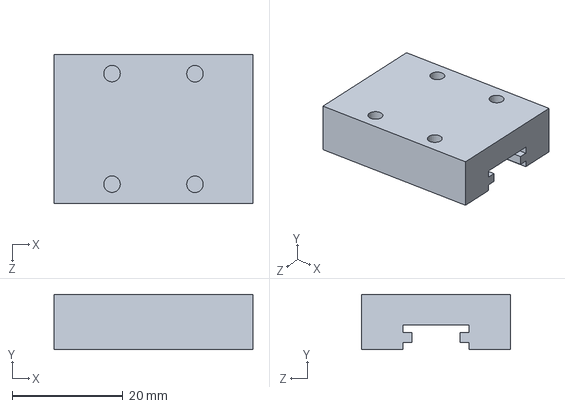
[picture p89: CAD file, 2019-07-11]
P3Steel XL MGN V19/P3Steel MGN XL/Source/MGN12C300/MGN12C300.SLDPRT
36.0 x 10.0 x 27.0 mm
