campy/P3Steel-MGN-V19-XL/P3Steel XL MGN V19/P3Steel MGN XL/Source/MGN12C400/MGN12C.SLDPRT

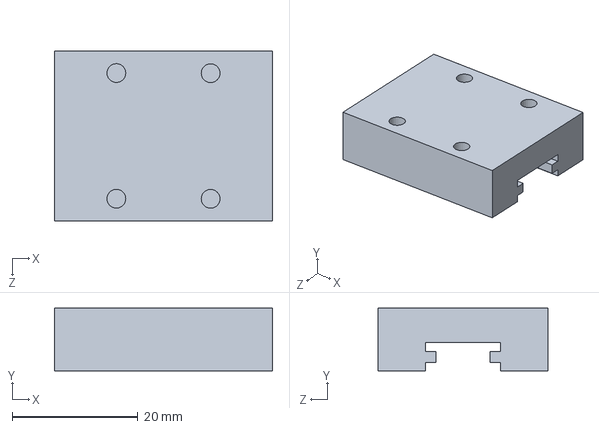
[picture p90: CAD file, 2019-09-07]
P3Steel XL MGN V19/P3Steel MGN XL/Source/MGN12C400/MGN12C.SLDPRT
34.7 x 10.0 x 27.0 mm
