campy/P3Steel-MGN-V19-XL/P3Steel XL MGN V19/P3Steel MGN XL/Source/Nema Y/Stepper motor/Part2.SLDPRT

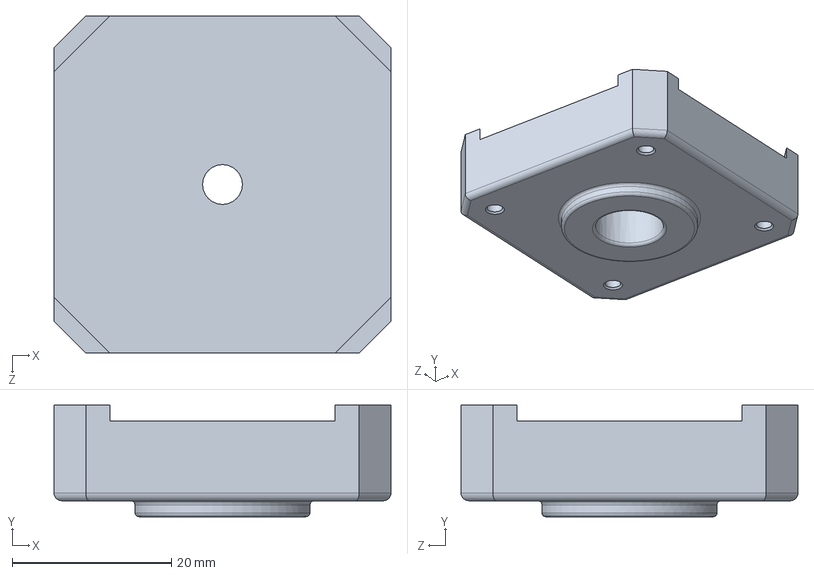
[picture p91: CAD file, 2019-07-11]
P3Steel XL MGN V19/P3Steel MGN XL/Source/Nema Y/Stepper motor/Part2.SLDPRT
42.3 x 14.0 x 42.3 mm
