campy/P3Steel-MGN-V19-XL/P3Steel XL MGN V19/P3Steel MGN XL/Source/Power Supply/MW_switching_25A.SLDPRT

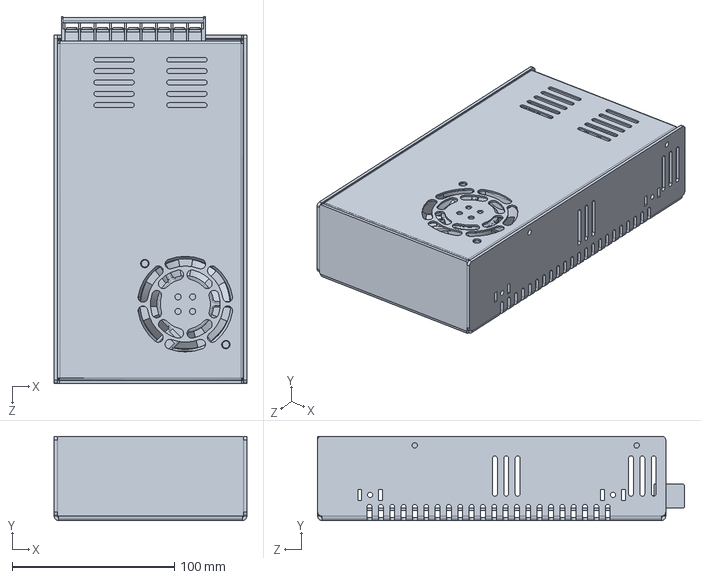
[picture p92: CAD file, 2019-09-07]
P3Steel XL MGN V19/P3Steel MGN XL/Source/Power Supply/MW_switching_25A.SLDPRT
119.0 x 52.0 x 226.5 mm
