campy/P3Steel-MGN-V19-XL/P3Steel XL MGN V19/P3Steel MGN XL/Source/Sraigtas ISO 7379 M4x15.SLDPRT

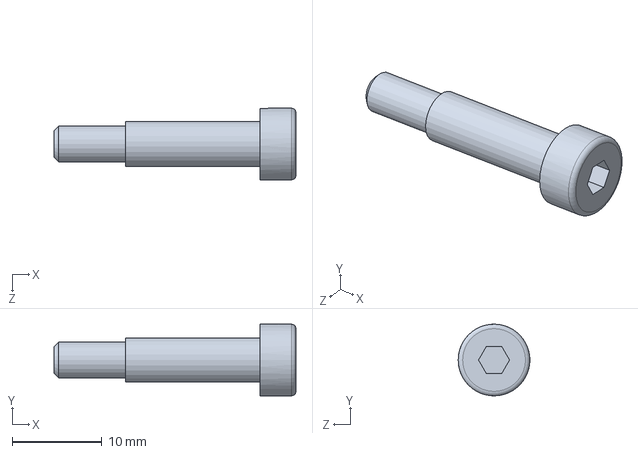
[picture p93: CAD file, 2019-09-13]
P3Steel XL MGN V19/P3Steel MGN XL/Source/Sraigtas ISO 7379 M4x15.SLDPRT
27.0 x 8.00 x 7.99 mm
