campy/P3Steel-MGN-V19-XL/P3Steel XL MGN V19/P3Steel MGN XL/Source/Titan Aero/Titan Aero P3steel/Radial Cooling Fan 50mm DC12V/turbine.SLDPRT

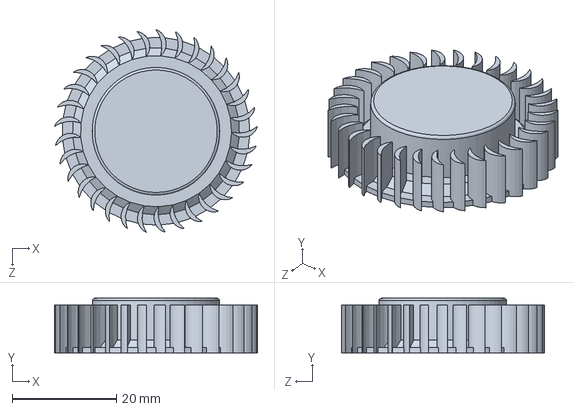
[picture p94: CAD file, 2019-07-11]
P3Steel XL MGN V19/P3Steel MGN XL/Source/Titan Aero/Titan Aero P3steel/Radial Cooling Fan 50mm DC12V/turbine.SLDPRT
39.0 x 10.5 x 38.9 mm
