campy/P3Steel-MGN-V19-XL/P3Steel XL MGN V19/P3Steel MGN XL/Source/Tuerca Anti-Back/napinacz nakretki tr8.stp

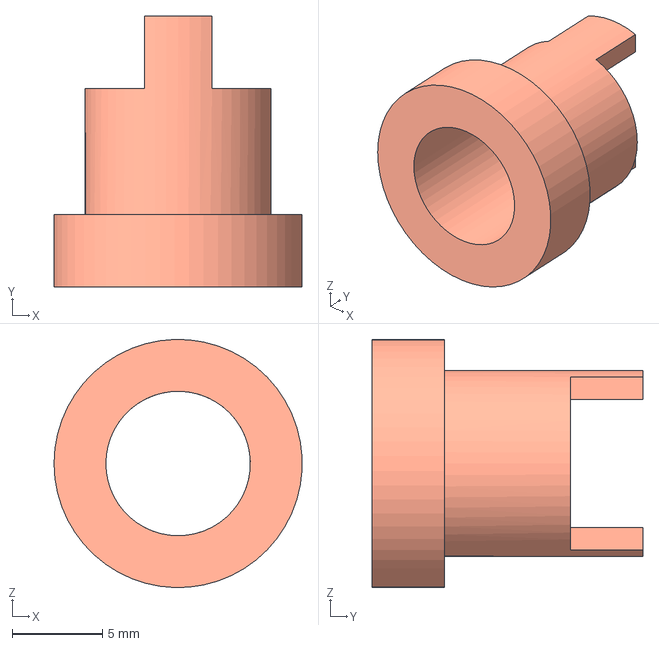
[picture p95: CAD file, 2019-07-11]
P3Steel XL MGN V19/P3Steel MGN XL/Source/Tuerca Anti-Back/napinacz nakretki tr8.stp
13.7 x 15.0 x 13.7 mm
