campy/P3Steel-MGN-V19-XL/P3Steel XL MGN V19/P3Steel MGN XL/Extrusor BMG+E3DV6/FAN DC12V 2510.SLDPRT

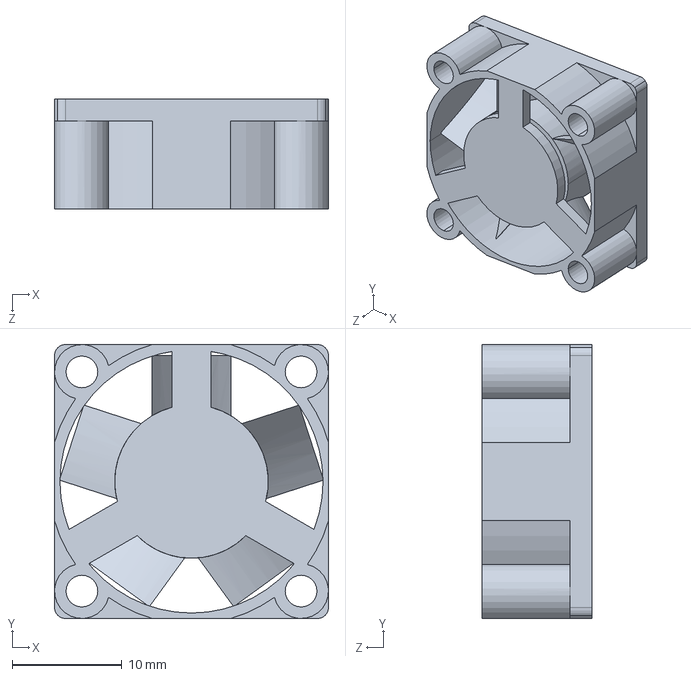
[picture p96: CAD file, 2019-09-19]
P3Steel XL MGN V19/P3Steel MGN XL/Extrusor BMG+E3DV6/FAN DC12V 2510.SLDPRT
25.0 x 25.0 x 10.0 mm
