campy/P3Steel-MGN-V19-XL/P3Steel XL MGN V19/P3Steel MGN XL/Extrusor BMG+Mosquito/LayerFanMosquito.SLDPRT

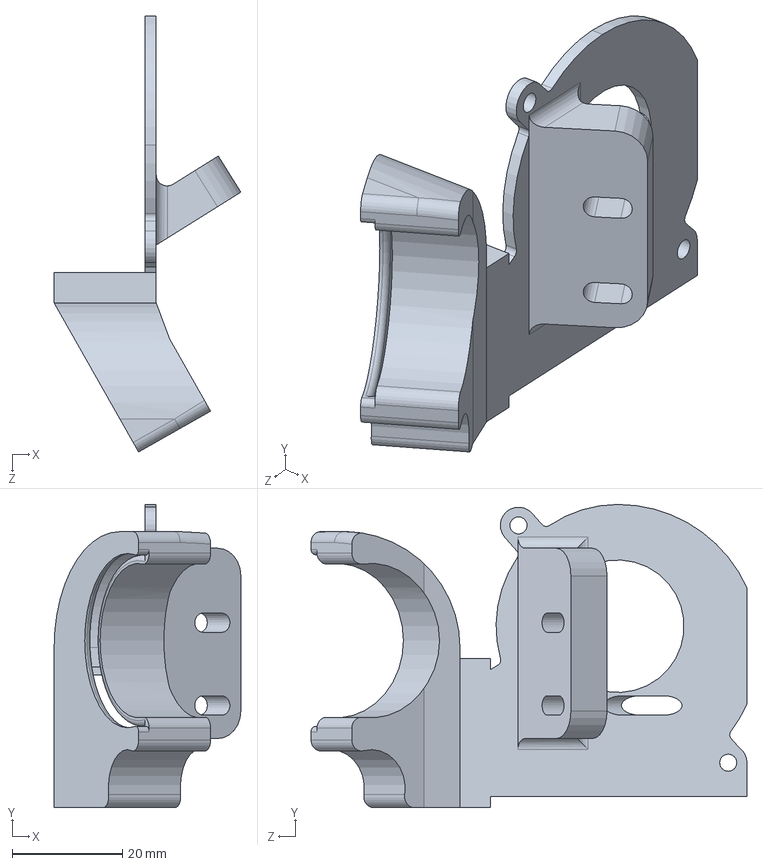
[picture p97: CAD file, 2019-10-11]
P3Steel XL MGN V19/P3Steel MGN XL/Extrusor BMG+Mosquito/LayerFanMosquito.SLDPRT
33.8 x 54.9 x 79.0 mm
