campy/P3Steel-MGN-V19-XL/P3Steel XL MGN V19/P3Steel MGN XL/Extrusor Titan Aero/LayerFanSupport-Titan.SLDPRT

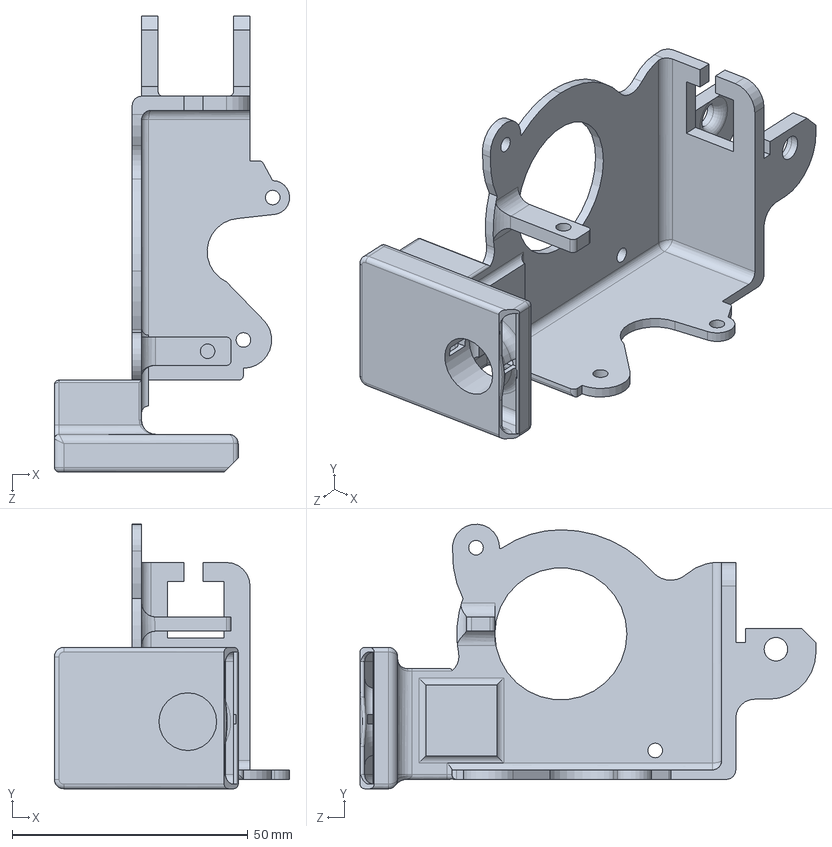
[picture p98: CAD file, 2019-09-19]
P3Steel XL MGN V19/P3Steel MGN XL/Extrusor Titan Aero/LayerFanSupport-Titan.SLDPRT
49.9 x 56.1 x 96.7 mm
