campy/P3Steel-MGN-V19-XL/P3Steel XL MGN V19/P3Steel MGN XL/Piezas impresas/Cadenetas/Cadeneta 5/Eslabon 5 Bloqueado.SLDPRT

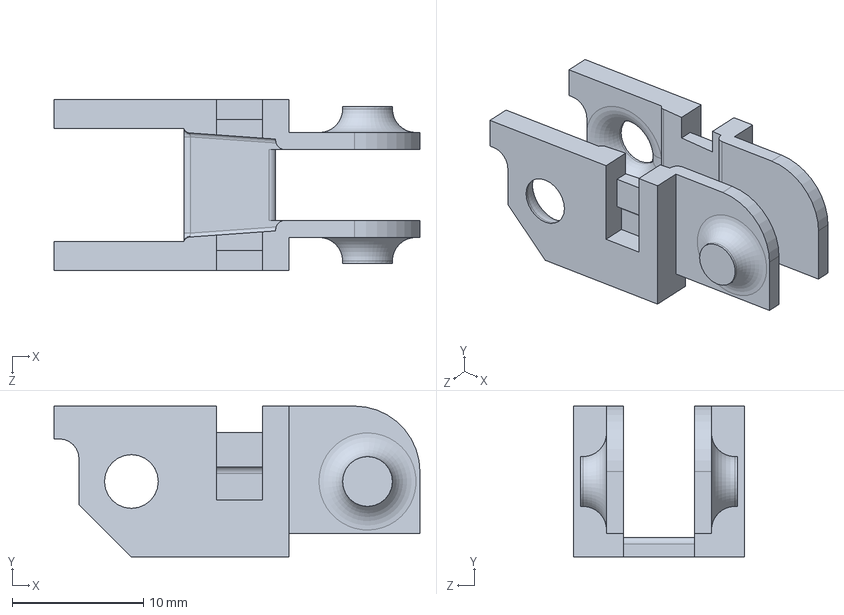
[picture p101: CAD file, 2019-09-07]
P3Steel XL MGN V19/P3Steel MGN XL/Piezas impresas/Cadenetas/Cadeneta 5/Eslabon 5 Bloqueado.SLDPRT
27.9 x 11.5 x 13.0 mm
