campy/P3Steel-MGN-V19-XL/P3Steel XL MGN V19/P3Steel MGN XL/Piezas impresas/Cadenetas/Cadeneta 5/Otros Tipos Eslabones/Soporte cama.SLDPRT

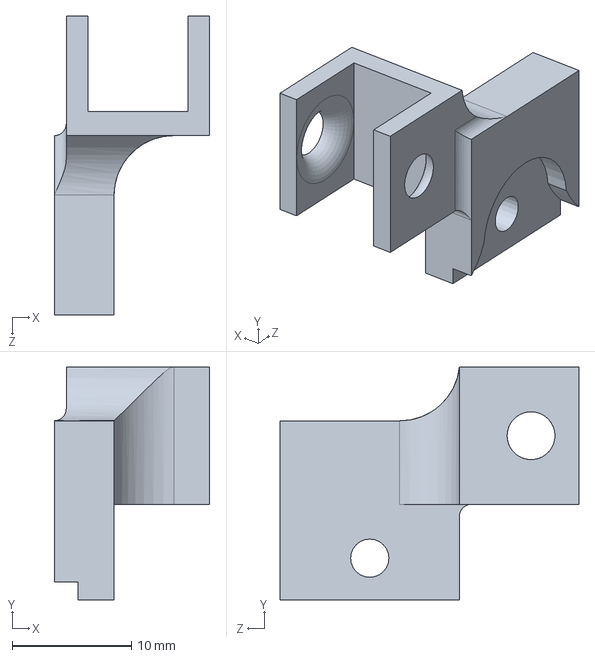
[picture p102: CAD file, 2019-07-11]
P3Steel XL MGN V19/P3Steel MGN XL/Piezas impresas/Cadenetas/Cadeneta 5/Otros Tipos Eslabones/Soporte cama.SLDPRT
13.0 x 19.5 x 25.0 mm
