campy/P3Steel-MGN-V19-XL/P3Steel XL MGN V19/P3Steel MGN XL/Piezas impresas/F-Sensor/Sensor filamento 2.0/Sensor filamento.SLDPRT

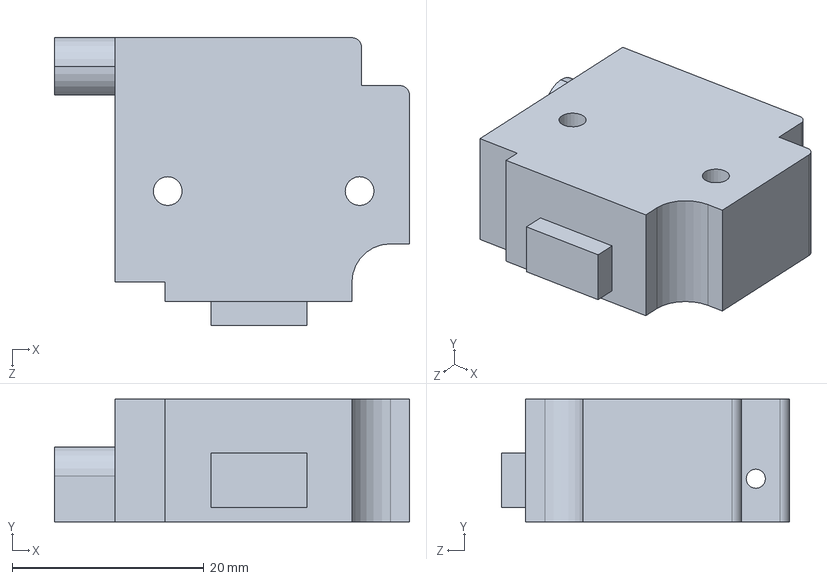
[picture p103: CAD file, 2019-09-07]
P3Steel XL MGN V19/P3Steel MGN XL/Piezas impresas/F-Sensor/Sensor filamento 2.0/Sensor filamento.SLDPRT
37.0 x 12.8 x 30.0 mm
