campy/P3Steel-MGN-V19-XL/P3Steel XL MGN V19/P3Steel MGN XL/Piezas impresas/LCD Cajas/Duet 5 Pulgadas/TapaCaja duet 5.SLDPRT

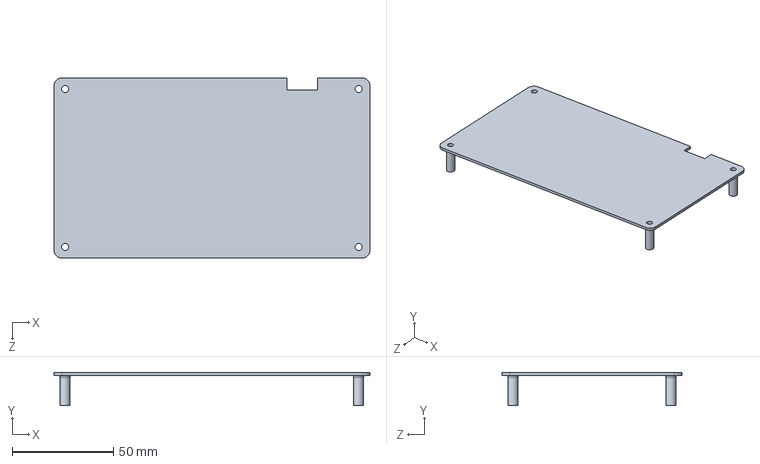
[picture p104: CAD file, 2019-11-12]
P3Steel XL MGN V19/P3Steel MGN XL/Piezas impresas/LCD Cajas/Duet 5 Pulgadas/TapaCaja duet 5.SLDPRT
156.0 x 16.5 x 89.0 mm
