campy/P3Steel-MGN-V19-XL/P3Steel XL MGN V19/P3Steel MGN XL/Piezas impresas/LCD Cajas/Duet 7 Pulgadas/Tapa.STL

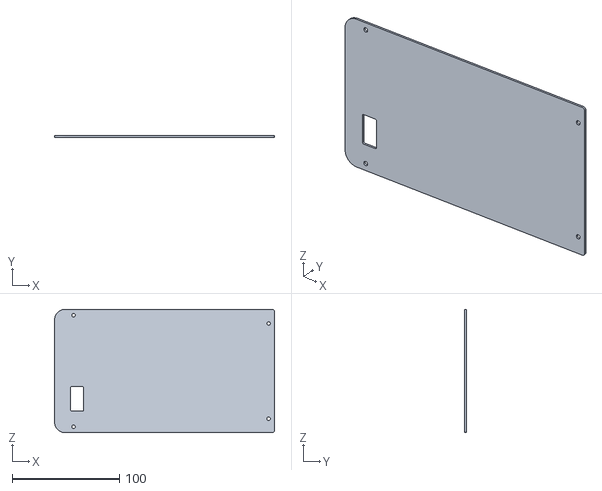
[picture p105: CAD file, 2019-07-11]
P3Steel XL MGN V19/P3Steel MGN XL/Piezas impresas/LCD Cajas/Duet 7 Pulgadas/Tapa.STL
205.0 x 1.50 x 115.0
