campy/P3Steel-MGN-V19-XL/P3Steel XL MGN V19/P3Steel MGN XL/Piezas impresas/LCD Cajas/Mini 12864 RGB inferior/tapa12864.SLDPRT

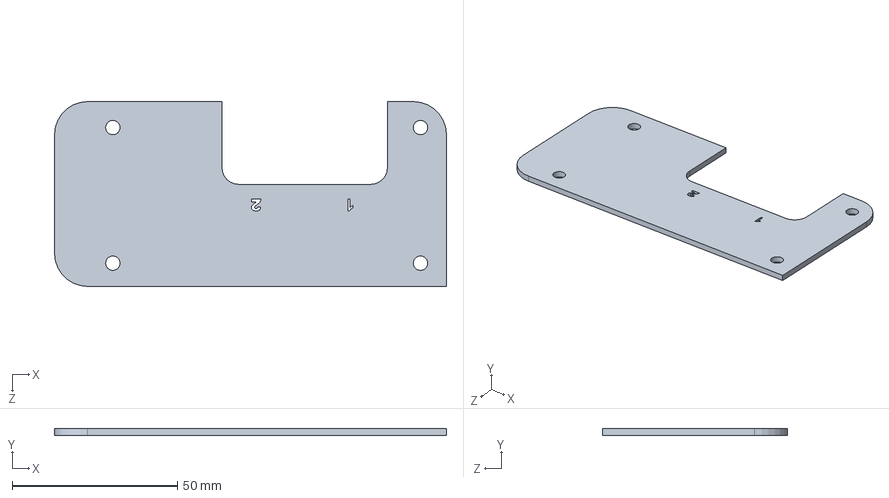
[picture p106: CAD file, 2020-01-10]
P3Steel XL MGN V19/P3Steel MGN XL/Piezas impresas/LCD Cajas/Mini 12864 RGB inferior/tapa12864.SLDPRT
118.5 x 2.00 x 55.9 mm
