campy/P3Steel-MGN-V19-XL/P3Steel XL MGN V19/P3Steel MGN XL/Piezas impresas/LCD Cajas/MKS12864 Soporte Marco/LCD Case support con apoyo.SLDPRT

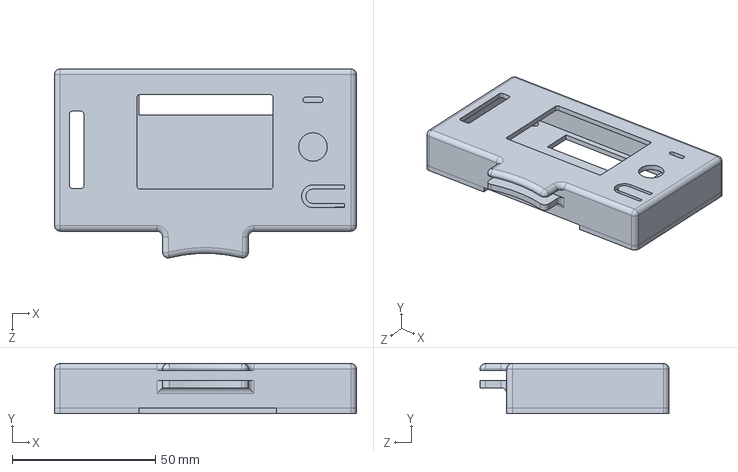
[picture p108: CAD file, 2019-07-11]
P3Steel XL MGN V19/P3Steel MGN XL/Piezas impresas/LCD Cajas/MKS12864 Soporte Marco/LCD Case support con apoyo.SLDPRT
105.5 x 17.5 x 66.0 mm
