campy/P3Steel-MGN-V19-XL/P3Steel XL MGN V19/P3Steel MGN XL/Piezas impresas/LCD Cajas/TFT 3.5 2en1/TFT35.SLDPRT

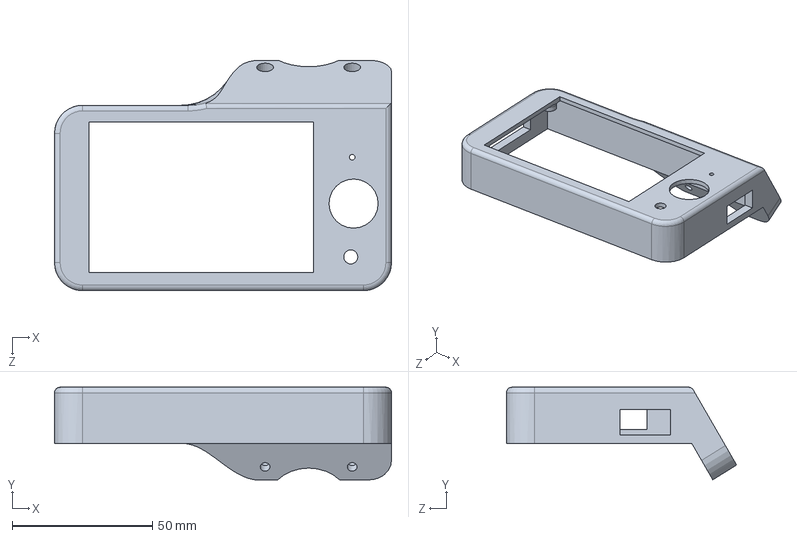
[picture p110: CAD file, 2020-01-10]
P3Steel XL MGN V19/P3Steel MGN XL/Piezas impresas/LCD Cajas/TFT 3.5 2en1/TFT35.SLDPRT
120.0 x 33.0 x 82.0 mm
