campy/P3Steel-MGN-V19-XL/P3Steel XL MGN V19/P3Steel MGN XL/Piezas impresas/Protectores ventiladores/60mm_crosshair_reduced_fan_cover.stl

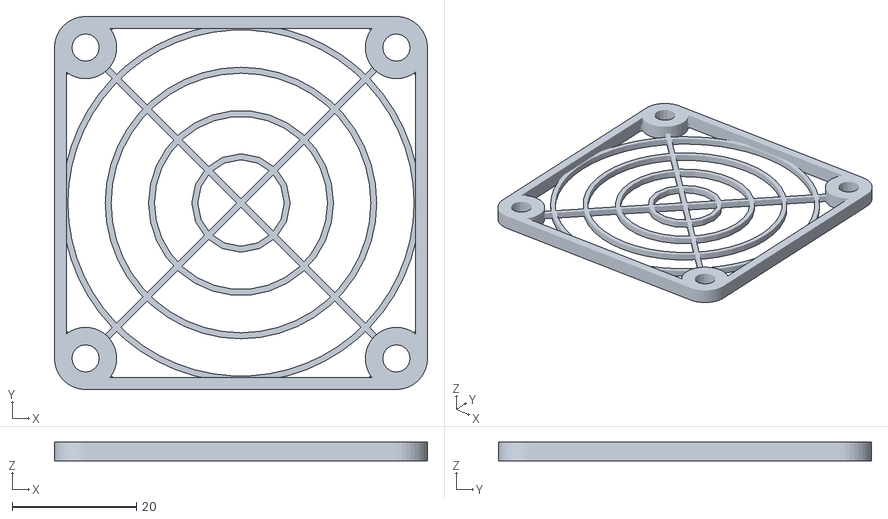
[picture p111: CAD file, 2019-07-11]
P3Steel XL MGN V19/P3Steel MGN XL/Piezas impresas/Protectores ventiladores/60mm_crosshair_reduced_fan_cover.stl
60.0 x 60.0 x 3.00
