campy/P3Steel-MGN-V19-XL/P3Steel XL MGN V19/P3Steel MGN XL/Piezas impresas/Raspberry box/Raspberry_Pi_B+_Sleeve_v2-1_CAP.STL

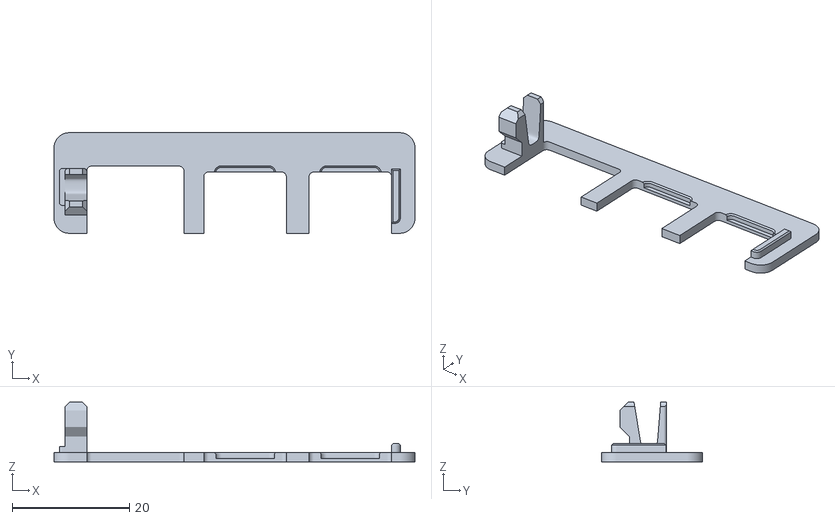
[picture p112: CAD file, 2019-07-11]
P3Steel XL MGN V19/P3Steel MGN XL/Piezas impresas/Raspberry box/Raspberry_Pi_B+_Sleeve_v2-1_CAP.STL
61.7 x 17.2 x 10.2
