campy/P3Steel-MGN-V19-XL/P3Steel XL MGN V19/P3Steel MGN XL/Piezas impresas/Soporte Correa Y.SLDPRT

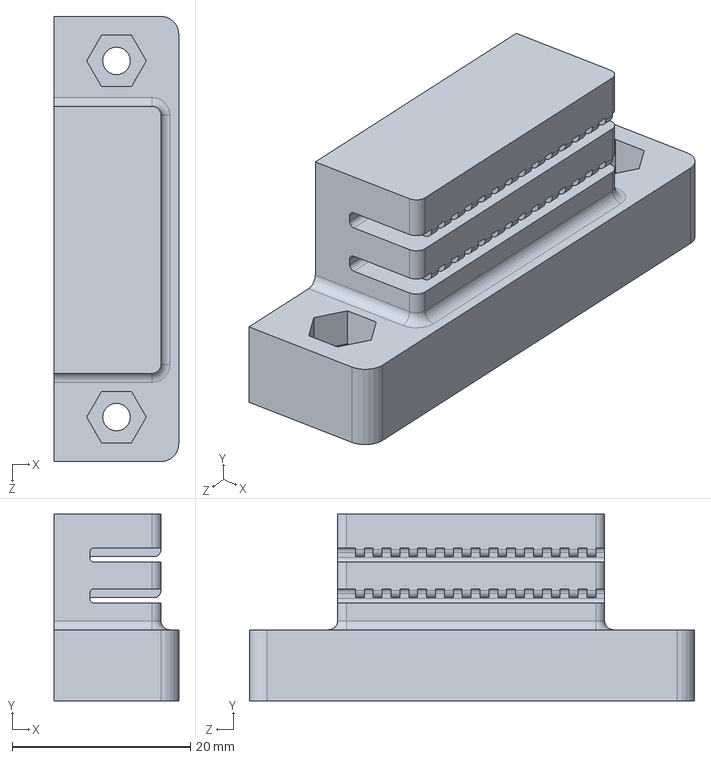
[picture p113: CAD file, 2020-01-10]
P3Steel XL MGN V19/P3Steel MGN XL/Piezas impresas/Soporte Correa Y.SLDPRT
14.0 x 21.0 x 50.0 mm
