campy/P3Steel-MGN-V19-XL/P3Steel XL MGN V19/P3Steel MGN XL/Piezas impresas/Soportes electronicas/Placas/SolidStateRelay_SSR-25DA.SLDPRT

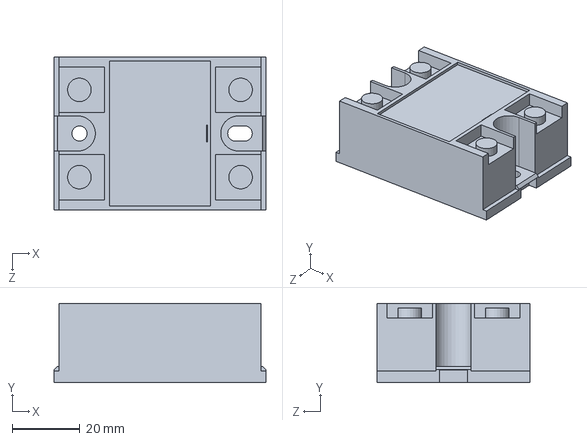
[picture p114: CAD file, 2019-07-11]
P3Steel XL MGN V19/P3Steel MGN XL/Piezas impresas/Soportes electronicas/Placas/SolidStateRelay_SSR-25DA.SLDPRT
62.7 x 23.4 x 45.2 mm
