campy/P3Steel-MGN-V19-XL/P3Steel XL MGN V19/P3Steel MGN XL/Piezas impresas/Soportes electronicas/Soporte MKSGENL-SKR13.SLDPRT

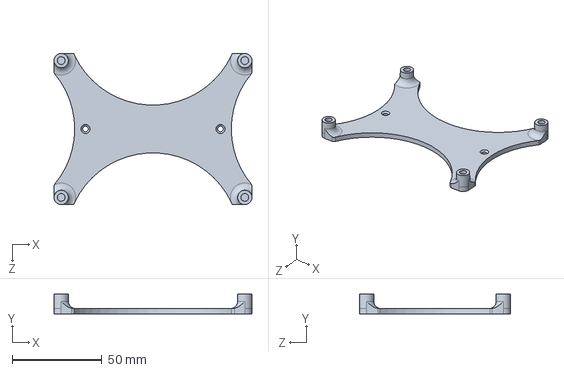
[picture p115: CAD file, 2019-09-07]
P3Steel XL MGN V19/P3Steel MGN XL/Piezas impresas/Soportes electronicas/Soporte MKSGENL-SKR13.SLDPRT
110.0 x 11.0 x 84.0 mm
