campy/P3Steel-MGN-V19-XL/P3Steel XL MGN V19/P3Steel MGN XL/Piezas impresas/Soportes electronicas/Tapa Electronica/Tapa Electronica SKR-Raspy.SLDPRT

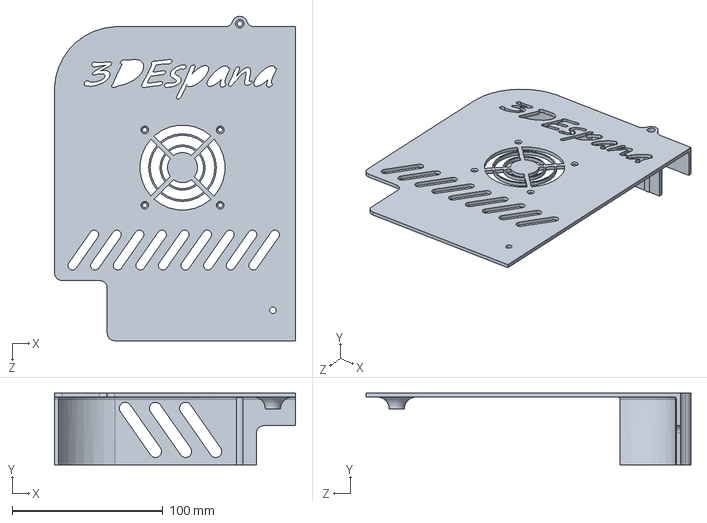
[picture p116: CAD file, 2019-09-07]
P3Steel XL MGN V19/P3Steel MGN XL/Piezas impresas/Soportes electronicas/Tapa Electronica/Tapa Electronica SKR-Raspy.SLDPRT
160.0 x 47.5 x 215.5 mm
