campy/P3Steel-MGN-V19-XL/P3Steel XL MGN V19/P3Steel MGN XL/Fotos ensamble/20191008_001711.jpg

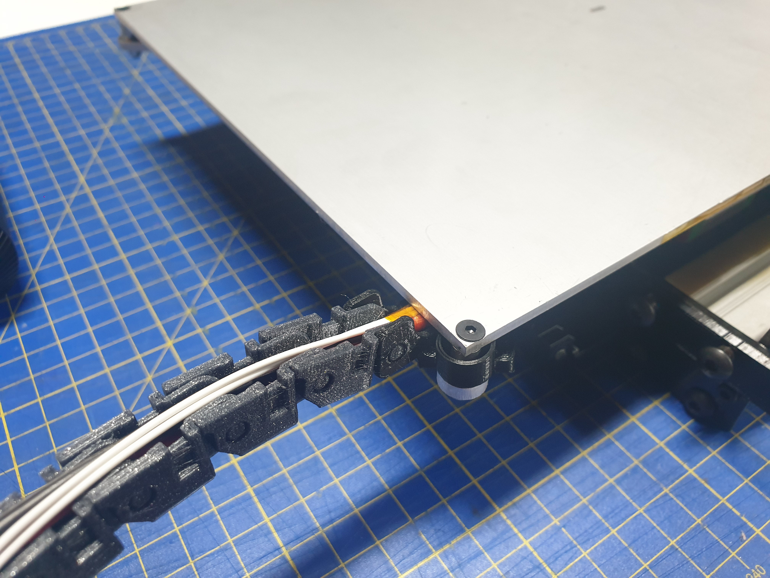
P3Steel XL MGN V19/P3Steel MGN XL/Fotos ensamble/20191008_001711.jpg
