campy/P3Steel-MGN-V19-XL/P3Steel XL MGN V19/P3Steel MGN XL/Fotos ensamble/20191009_201432.jpg

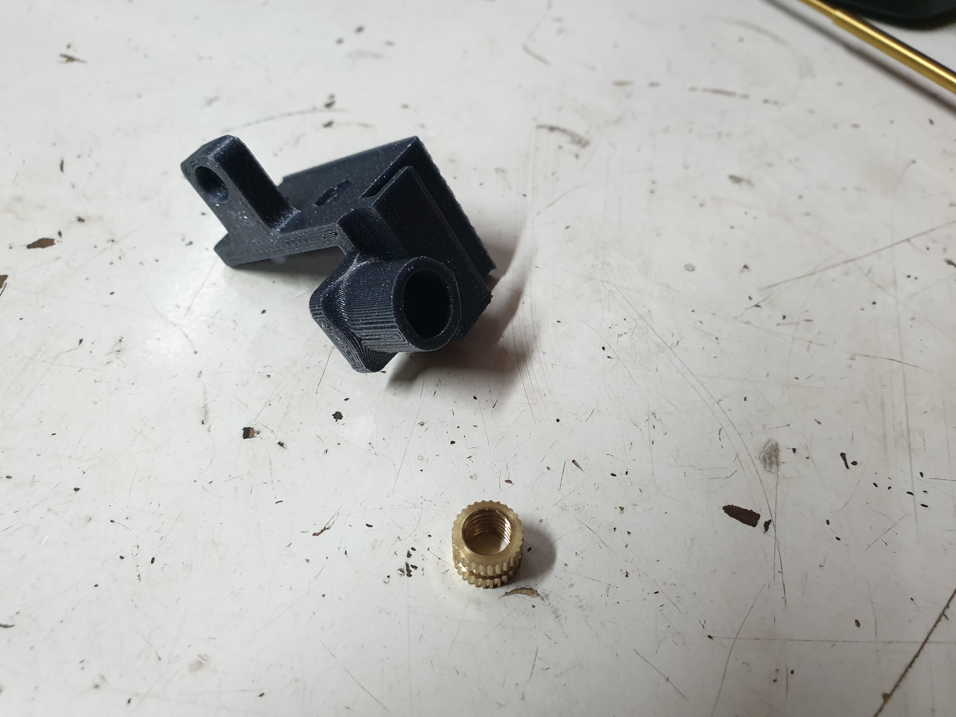
P3Steel XL MGN V19/P3Steel MGN XL/Fotos ensamble/20191009_201432.jpg
